lukacslacko/rolling_clock/designs/rolling-timer-p1s-light/bob-1mm/comparison-cad.png

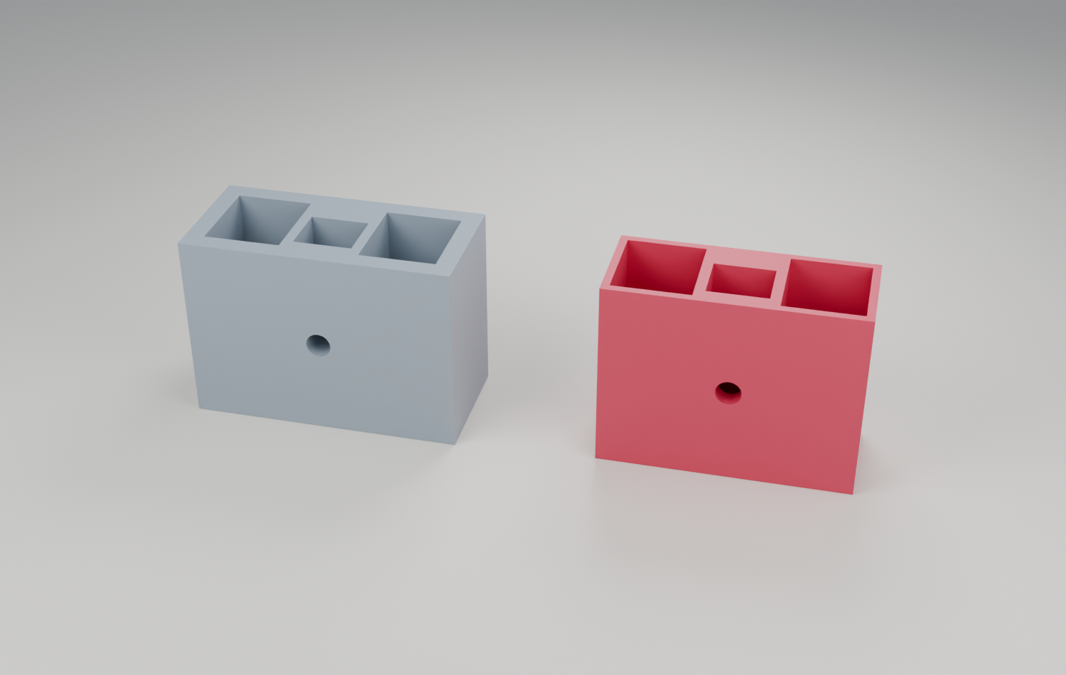
designs/rolling-timer-p1s-light/bob-1mm/comparison-cad.png
