lukacslacko/rolling_clock/designs/rolling-timer-p1s-light/bowl-bolt-section.png

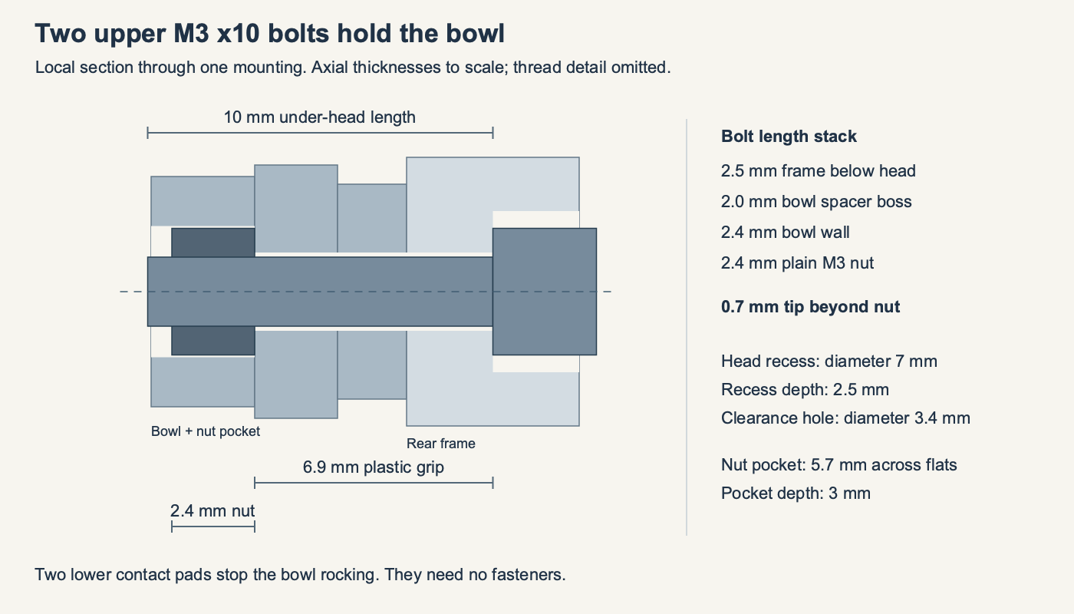
designs/rolling-timer-p1s-light/bowl-bolt-section.png
