lukacslacko/rolling_clock/designs/rolling-timer-p1s-light/fit-coupon.png

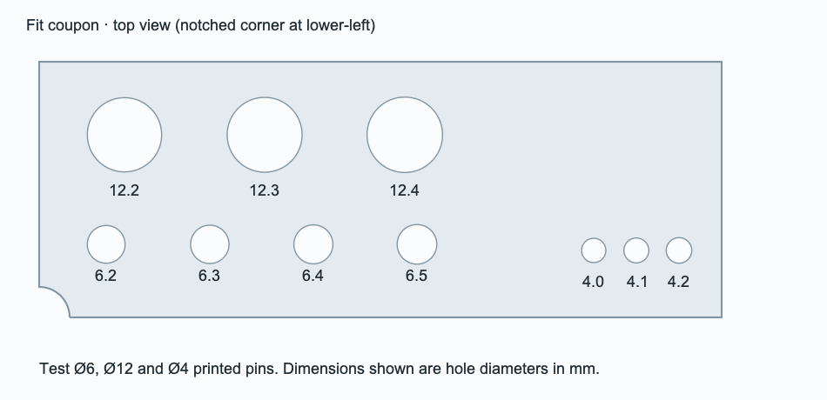
designs/rolling-timer-p1s-light/fit-coupon.png
