lukacslacko/rolling_clock/designs/rolling-timer-p1s-light/renders/light-mechanism.png

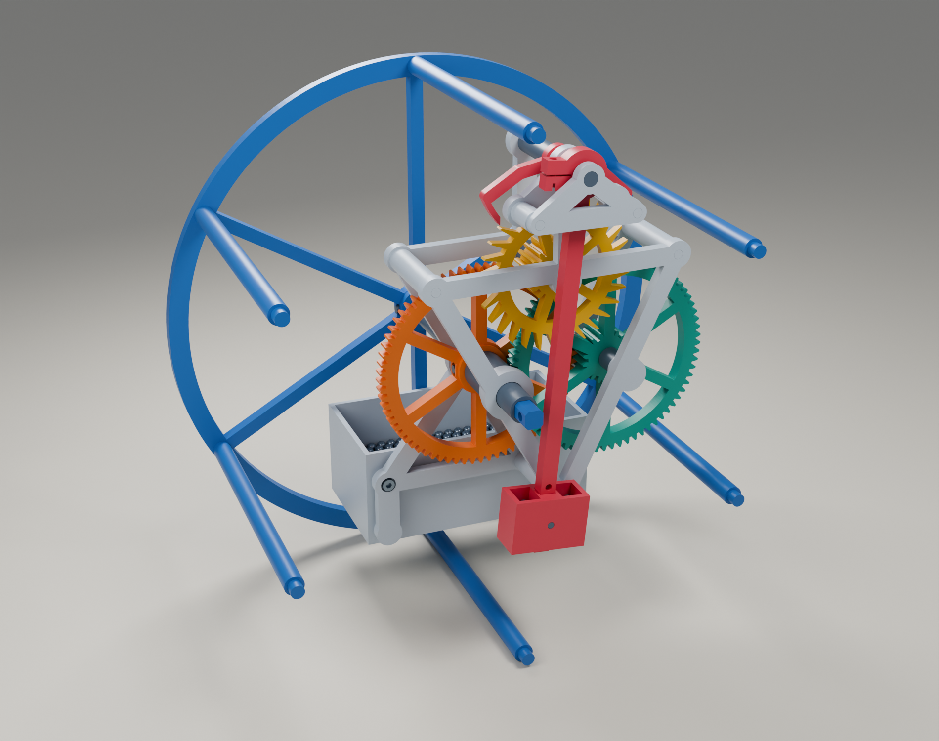
designs/rolling-timer-p1s-light/renders/light-mechanism.png
