lukacslacko/rolling_clock/designs/rolling-timer-p1s-light/renders/light-rear.png

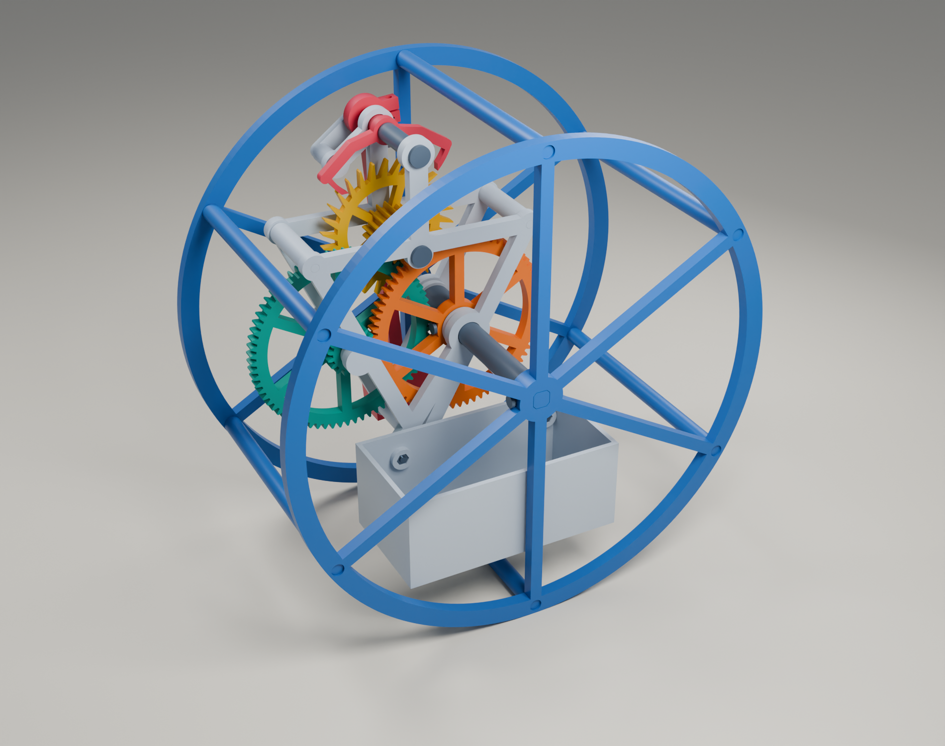
designs/rolling-timer-p1s-light/renders/light-rear.png
