lukacslacko/rolling_clock/designs/rolling-timer-p1s-r2/mounting-layout.png

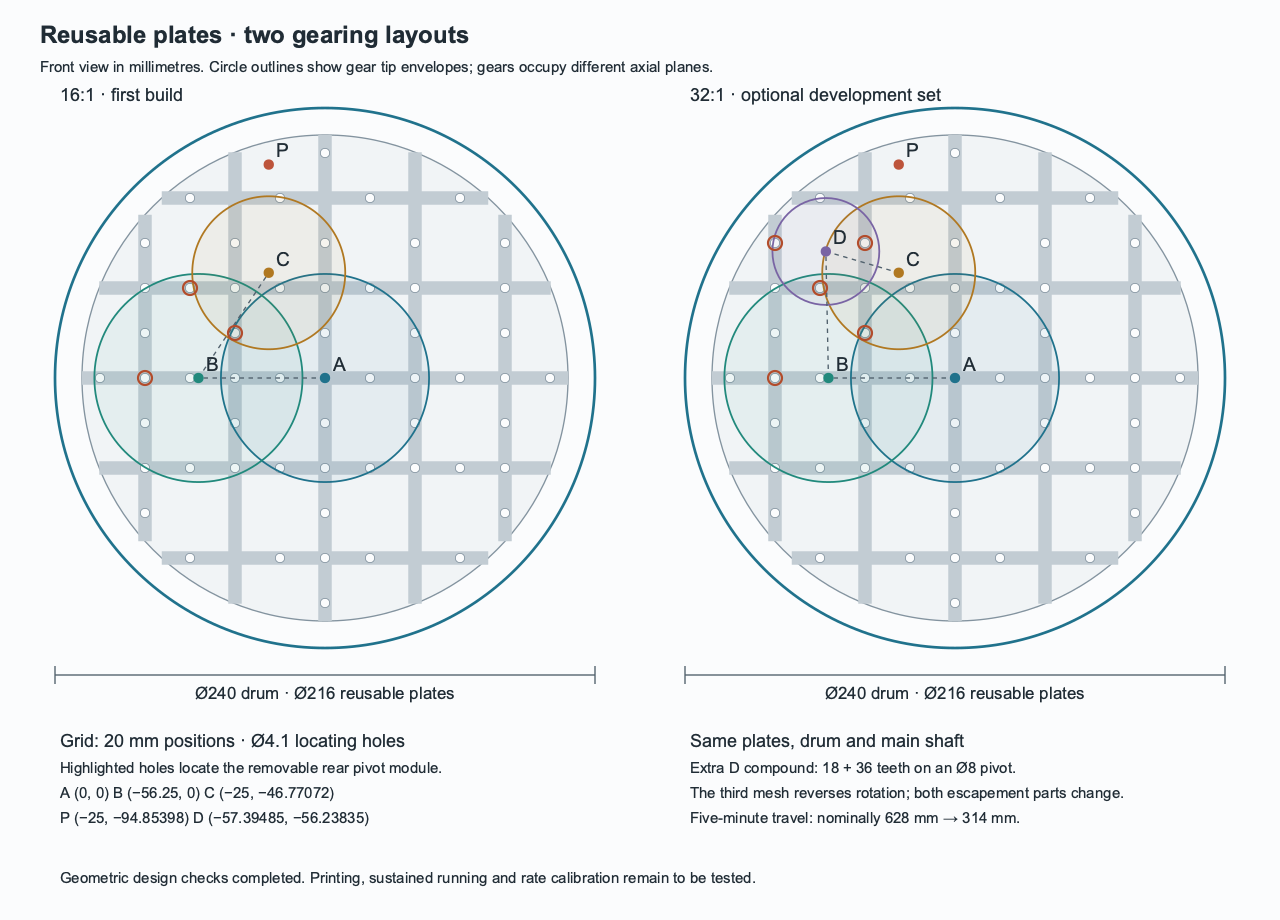
designs/rolling-timer-p1s-r2/mounting-layout.png
