lukacslacko/rolling_clock/designs/rolling-timer-p1s-r2/renders/perspective-rear.png

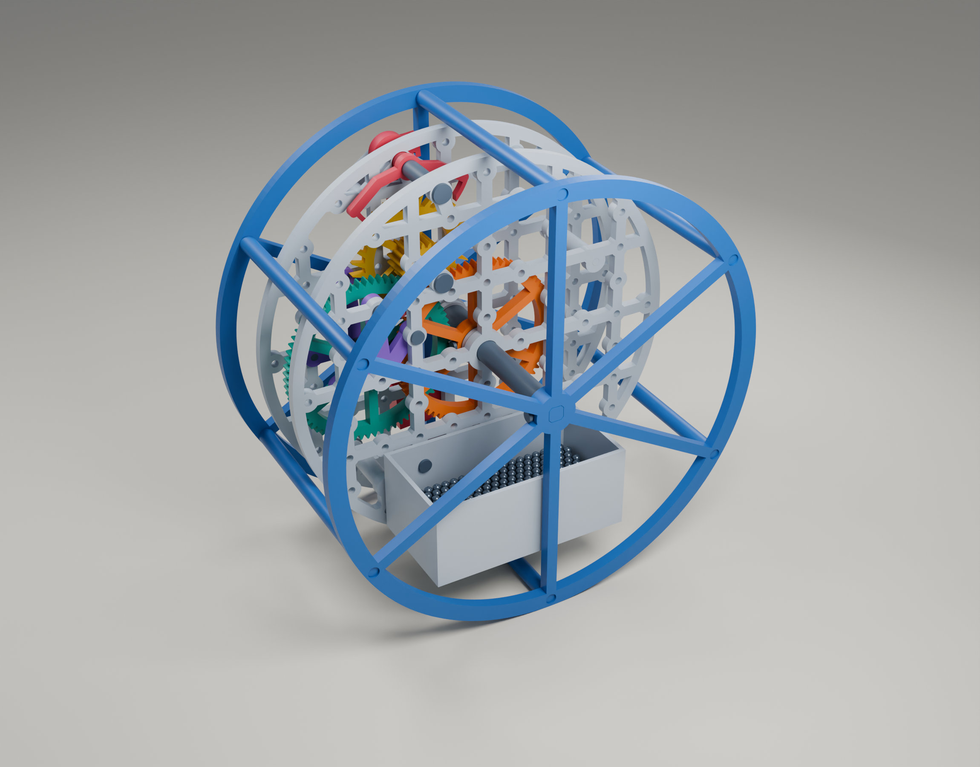
designs/rolling-timer-p1s-r2/renders/perspective-rear.png
