lukacslacko/rolling_clock/designs/rolling-timer-r3/renders/axle-detail.png

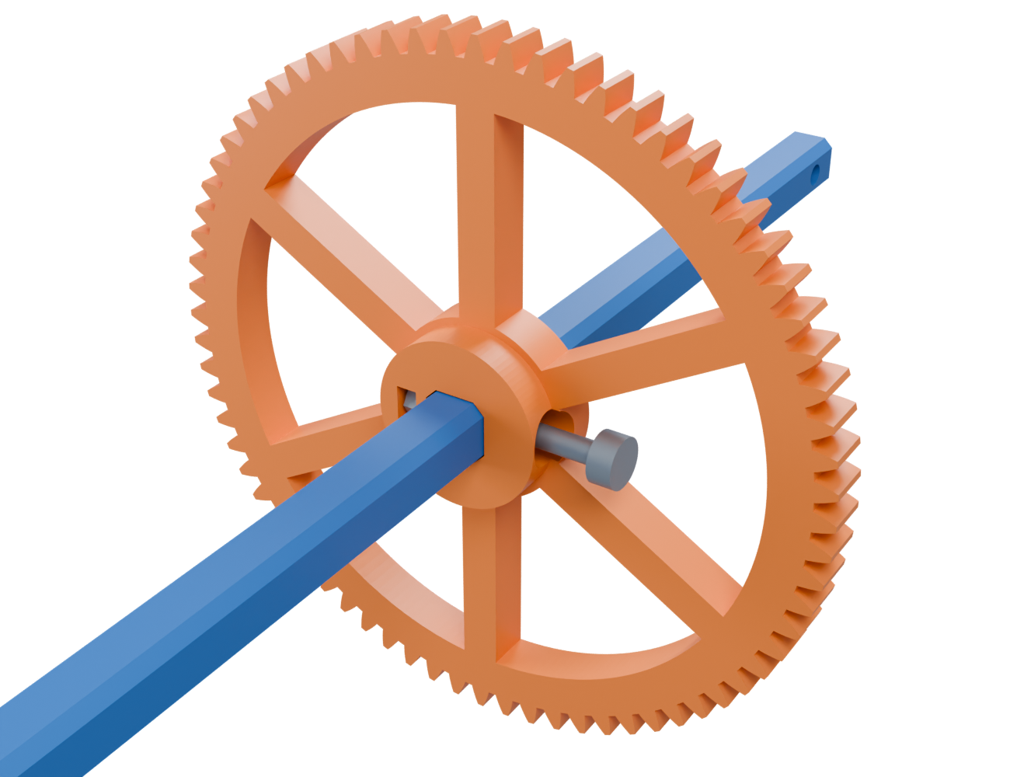
designs/rolling-timer-r3/renders/axle-detail.png
