lukacslacko/rolling_clock/designs/rolling-timer-r3/renders/bob-front-detail.png

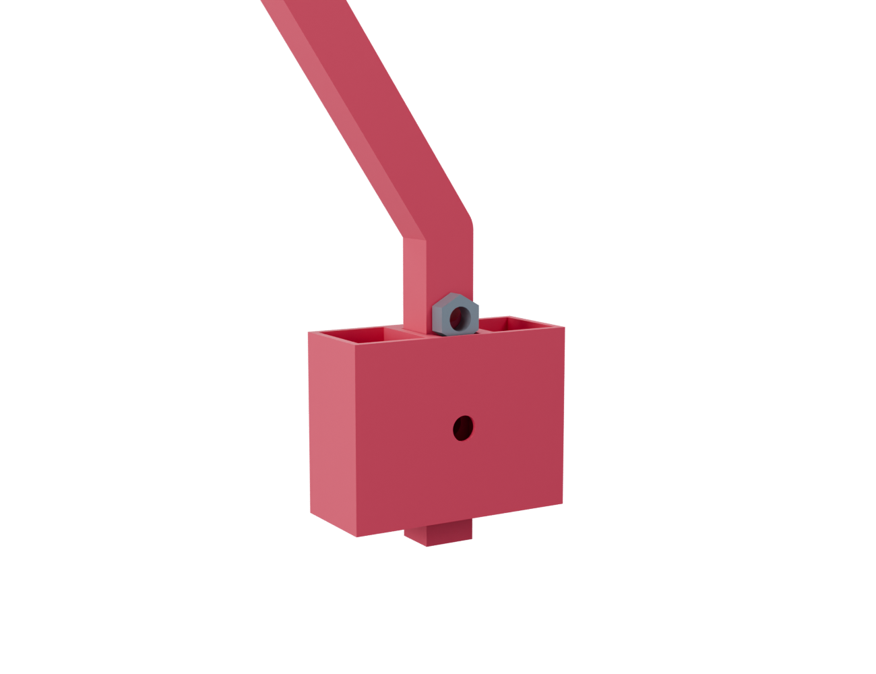
designs/rolling-timer-r3/renders/bob-front-detail.png
