lukacslacko/rolling_clock/designs/rolling-timer-r3/renders/case-post-detail.png

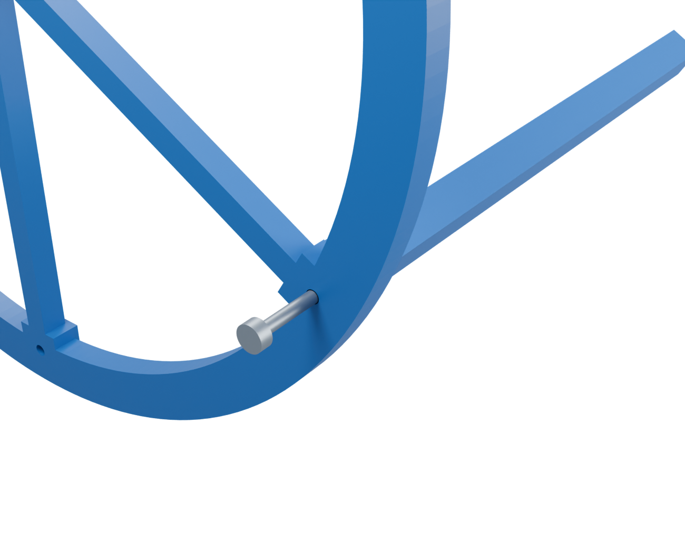
designs/rolling-timer-r3/renders/case-post-detail.png
