lukacslacko/rolling_clock/designs/rolling-timer-r3/renders/front-and-pendulum.png

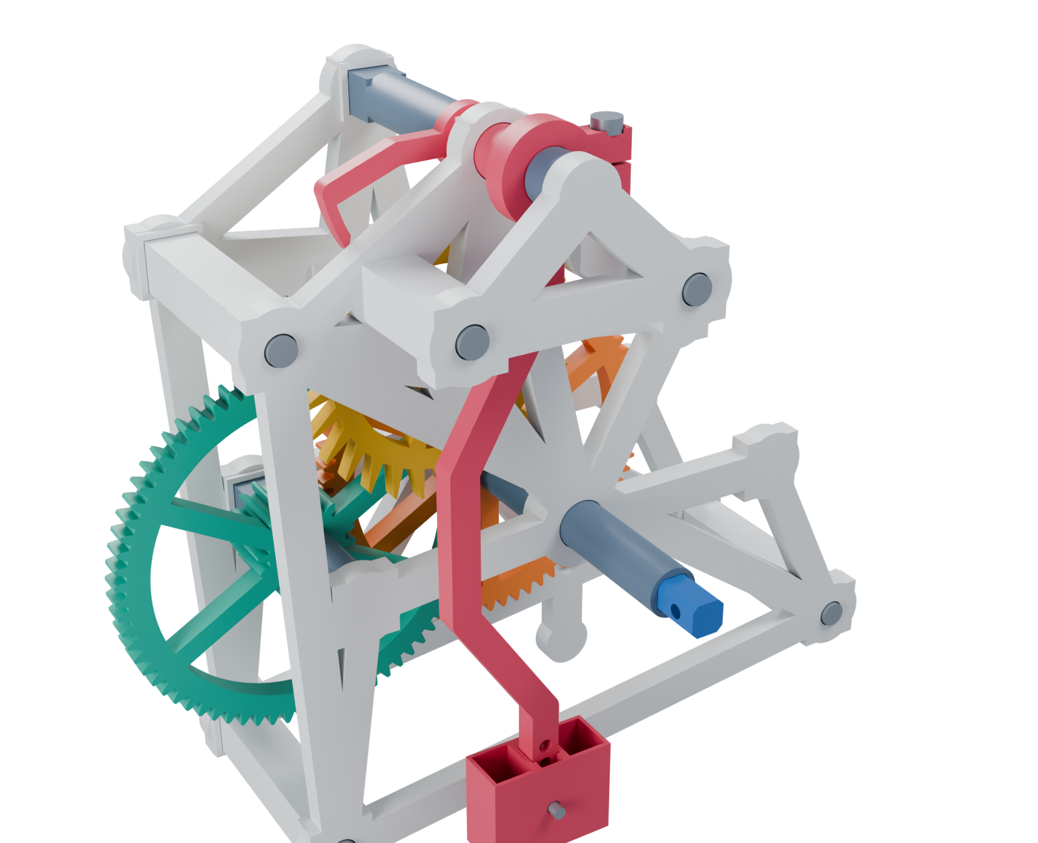
designs/rolling-timer-r3/renders/front-and-pendulum.png
