lukacslacko/rolling_clock/designs/rolling-timer-r3/renders/gear-stack.png

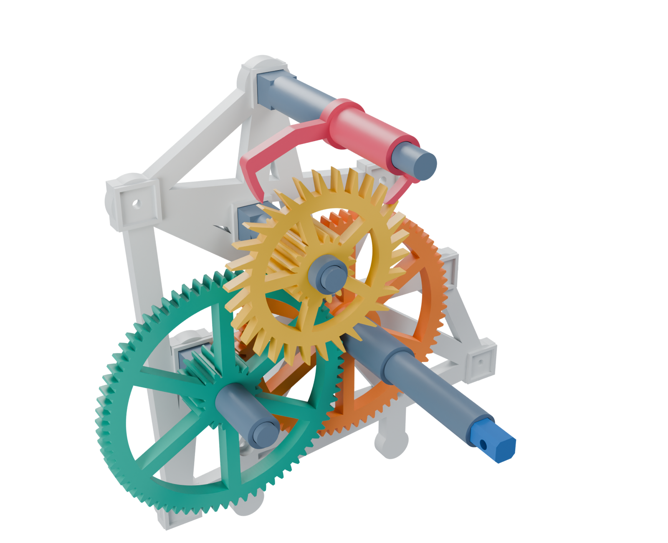
designs/rolling-timer-r3/renders/gear-stack.png
