lukacslacko/rolling_clock/designs/rolling-timer-r3/renders/mechanism-16x.png

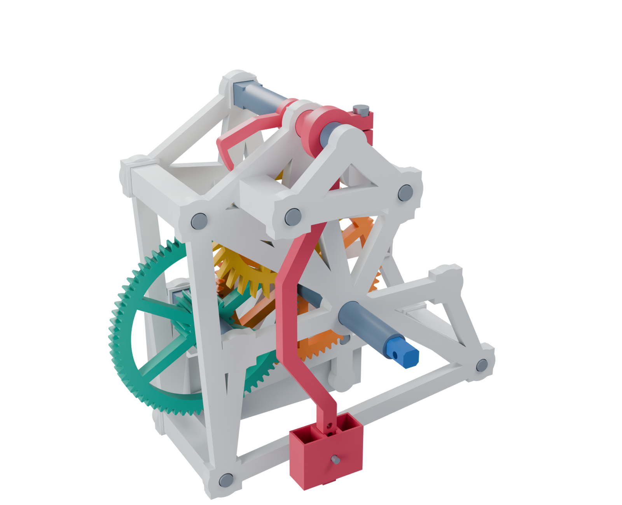
designs/rolling-timer-r3/renders/mechanism-16x.png
