lukacslacko/rolling_clock/designs/rolling-timer-p1s-r2/renders/square-drive-components.png

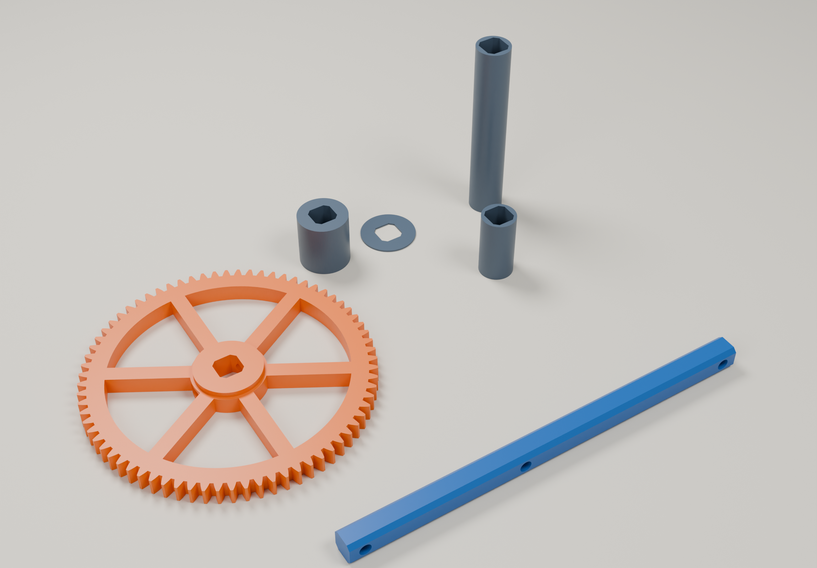
designs/rolling-timer-p1s-r2/renders/square-drive-components.png
