lukacslacko/rolling_clock/designs/rolling-timer-p1s-light/STL/30_fit_test_4mm.stl

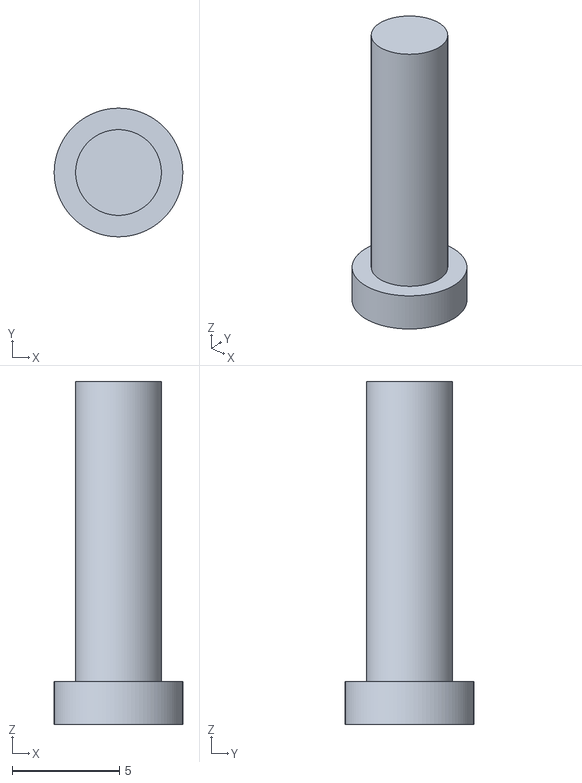
[picture p34: CAD file, 2026-10-01]
designs/rolling-timer-p1s-light/STL/30_fit_test_4mm.stl
6.00 x 6.00 x 16.0
