lukacslacko/rolling_clock/designs/rolling-timer-p1s-r2/source/assembly/24_11_compound_18_72.stl

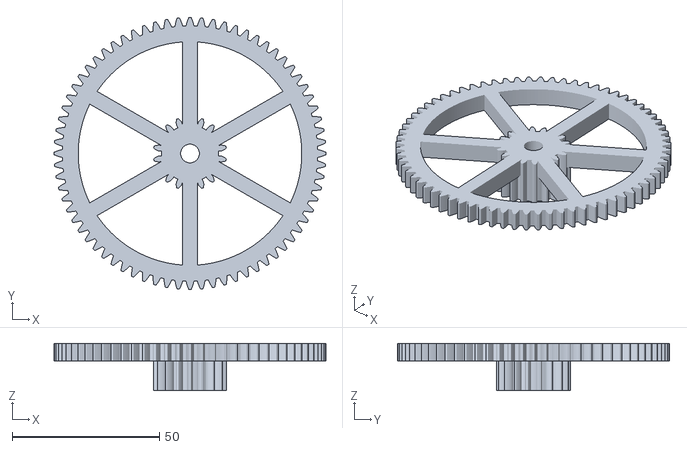
[picture p35: CAD file, 2026-10-01]
designs/rolling-timer-p1s-r2/source/assembly/24_11_compound_18_72.stl
92.5 x 92.5 x 16.0
