lukacslacko/rolling_clock/designs/rolling-timer-p1s-r2/upgrade-32x/STL/U11_D_recessed_collar.stl

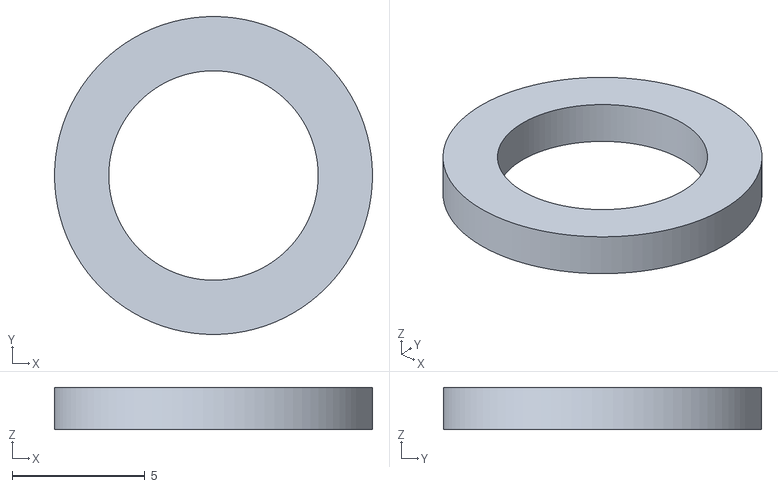
[picture p36: CAD file, 2026-10-01]
designs/rolling-timer-p1s-r2/upgrade-32x/STL/U11_D_recessed_collar.stl
12.0 x 12.0 x 1.60
