lukacslacko/rolling_clock/designs/rolling-timer-r3/assembly/16x/01_front_case_wheel.stl

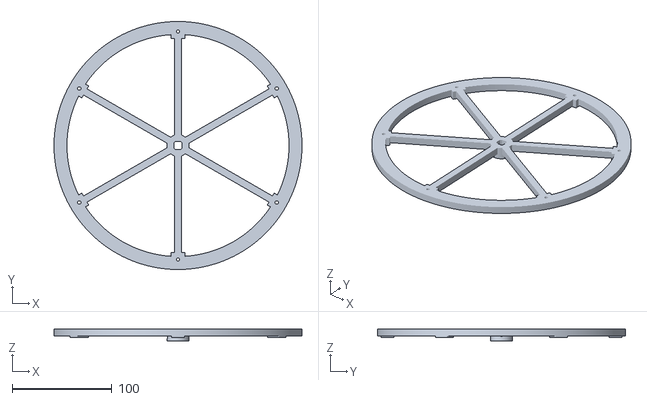
[picture p37: CAD file, 2026-10-08]
designs/rolling-timer-r3/assembly/16x/01_front_case_wheel.stl
248.0 x 248.0 x 12.0
