lukacslacko/rolling_clock/designs/rolling-timer-r3/STL/16x/11_B_18_72.stl

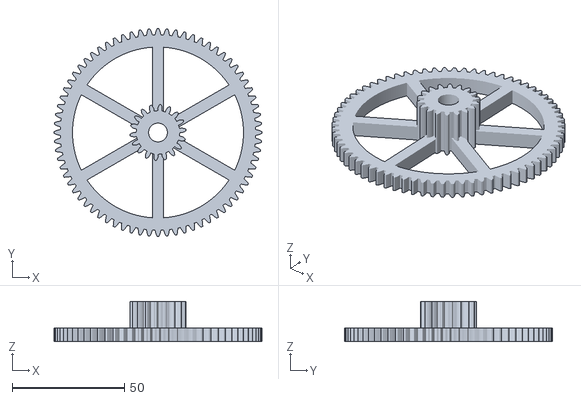
[picture p38: CAD file, 2026-10-02]
designs/rolling-timer-r3/STL/16x/11_B_18_72.stl
92.5 x 92.5 x 18.0
