lukacslacko/rolling_clock/designs/rolling-timer-r3/STL/32x/27_C_front_spacer.stl

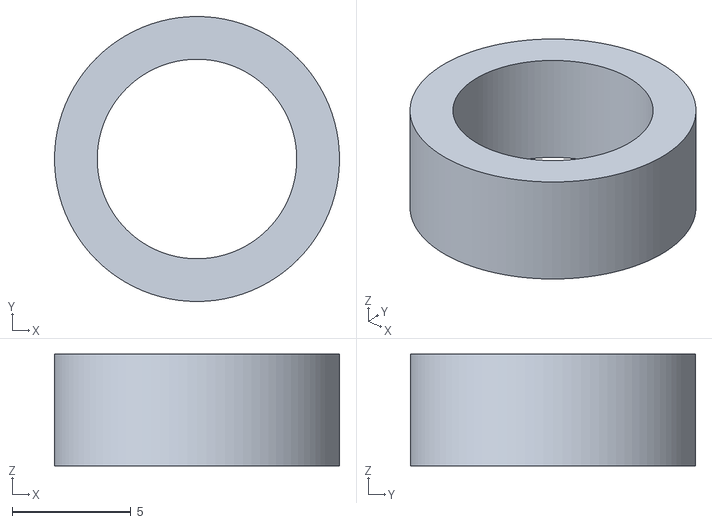
[picture p39: CAD file, 2026-10-02]
designs/rolling-timer-r3/STL/32x/27_C_front_spacer.stl
12.0 x 12.0 x 4.70
