lukacslacko/rolling_clock/designs/rolling-timer-r3/STL/slow-common/18_anchor_reversed.stl

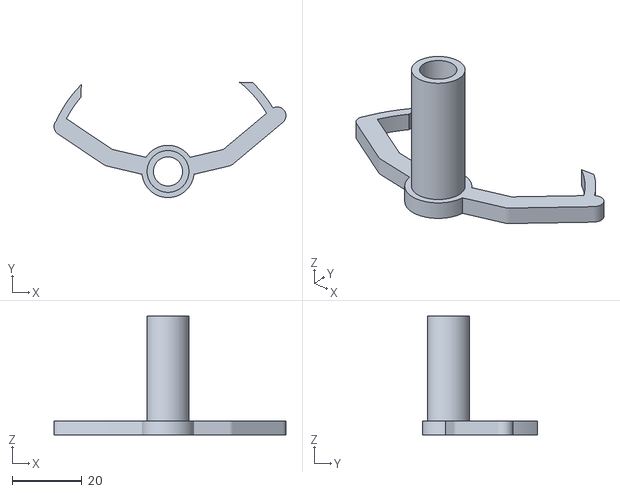
[picture p40: CAD file, 2026-10-02]
designs/rolling-timer-r3/STL/slow-common/18_anchor_reversed.stl
66.5 x 33.0 x 34.0
