lukacslacko/rolling_clock/designs/rolling-timer-p1s-light/bob-1mm/25_open_pendulum_bob_1mm.stl

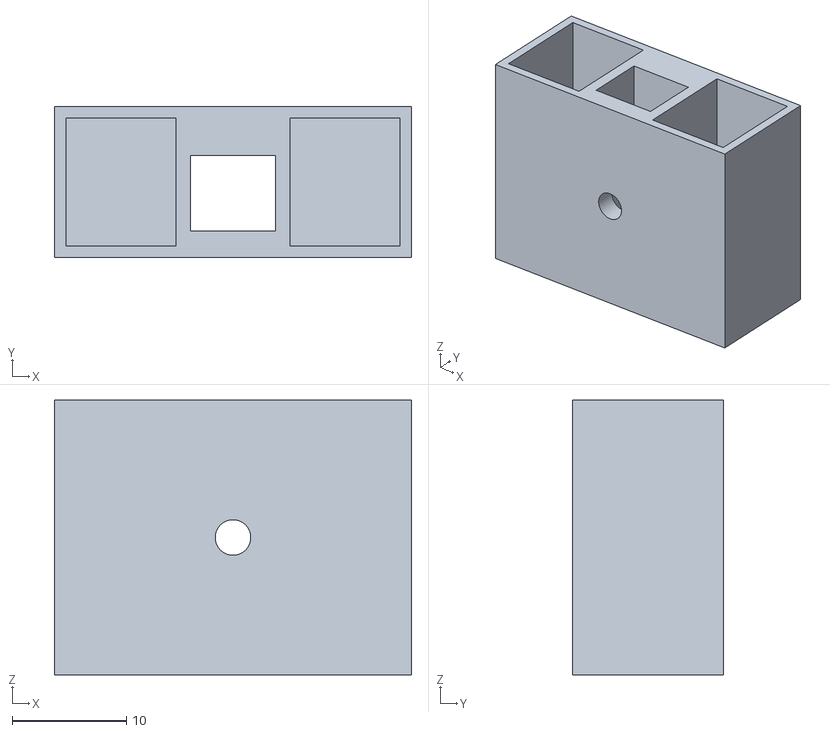
[picture p41: CAD file, 2026-10-01]
designs/rolling-timer-p1s-light/bob-1mm/25_open_pendulum_bob_1mm.stl
31.2 x 13.2 x 24.0
