lukacslacko/rolling_clock/designs/rolling-timer-p1s-light/source/assembly/03_02_case_post.stl

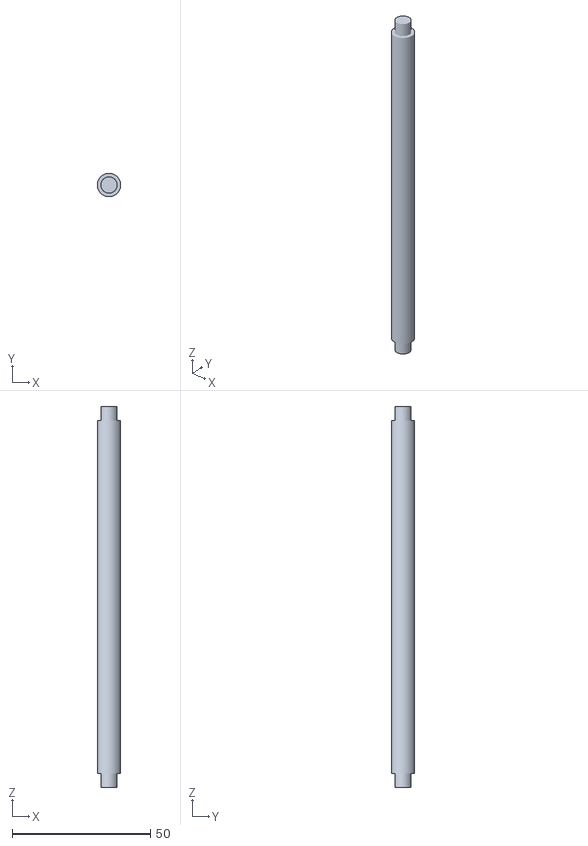
[picture p42: CAD file, 2026-10-01]
designs/rolling-timer-p1s-light/source/assembly/03_02_case_post.stl
8.50 x 8.50 x 138.0
