lukacslacko/rolling_clock/designs/rolling-timer-p1s-light/STL/01_case_wheel.stl

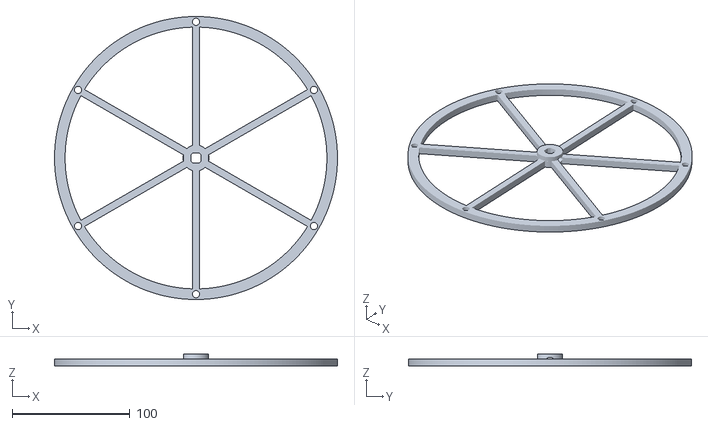
[picture p43: CAD file, 2026-10-01]
designs/rolling-timer-p1s-light/STL/01_case_wheel.stl
240.0 x 240.0 x 10.0
