lukacslacko/rolling_clock/designs/rolling-timer-p1s-r2/source/assembly/27_31_B_rear_pivot_module.stl

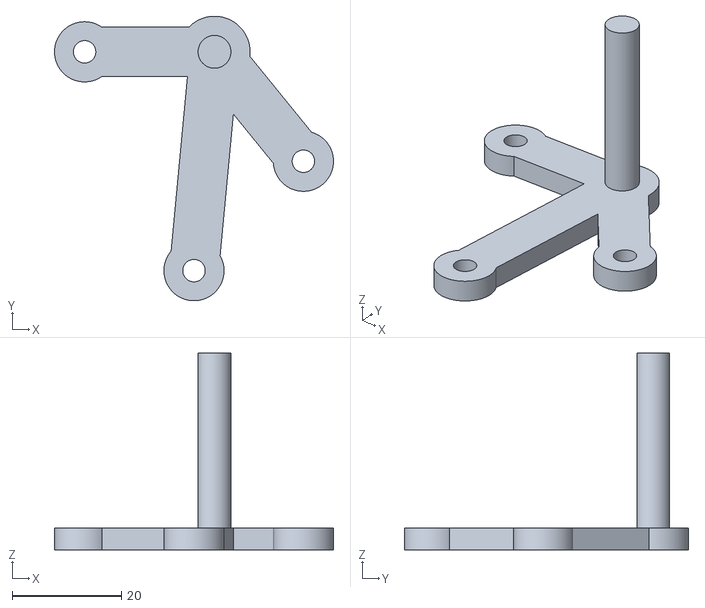
[picture p44: CAD file, 2026-10-01]
designs/rolling-timer-p1s-r2/source/assembly/27_31_B_rear_pivot_module.stl
51.0 x 52.0 x 36.0
