lukacslacko/rolling_clock/designs/rolling-timer-p1s-r2/STL/27_fit_coupon.stl

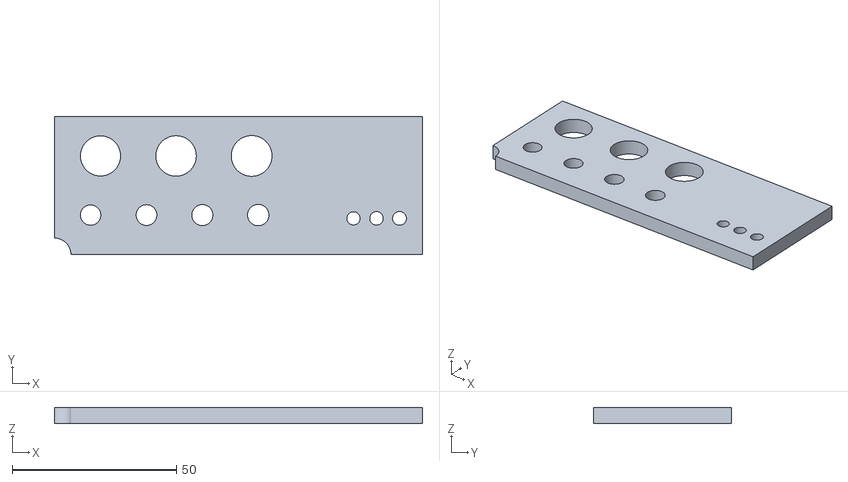
[picture p45: CAD file, 2026-10-01]
designs/rolling-timer-p1s-r2/STL/27_fit_coupon.stl
112.0 x 42.0 x 5.00
