lukacslacko/rolling_clock/designs/rolling-timer-p1s-r2/upgrade-32x/STL/U10_D_rear_spacer.stl

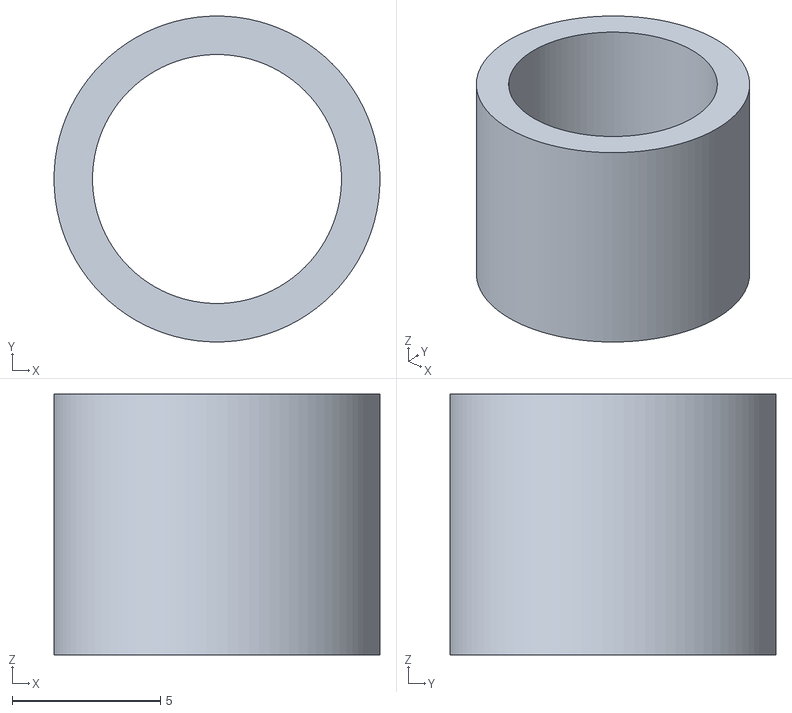
[picture p46: CAD file, 2026-10-01]
designs/rolling-timer-p1s-r2/upgrade-32x/STL/U10_D_rear_spacer.stl
11.0 x 11.0 x 8.80
