lukacslacko/rolling_clock/designs/rolling-timer-r3/STL/64x/12_escape_compound.stl

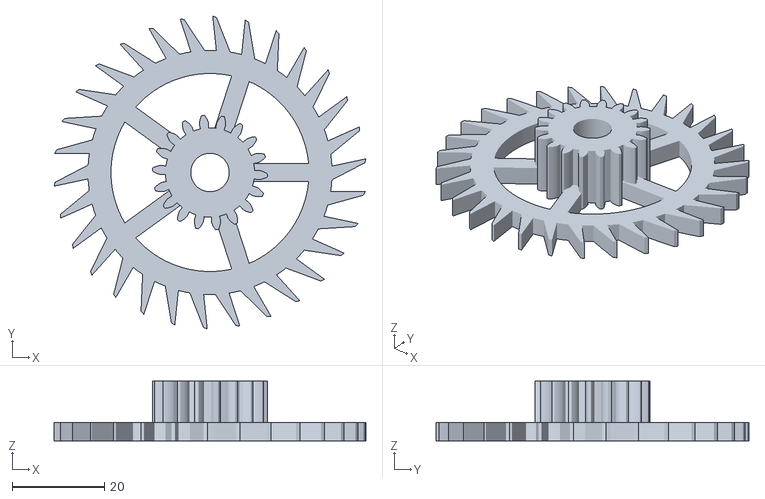
[picture p47: CAD file, 2026-10-02]
designs/rolling-timer-r3/STL/64x/12_escape_compound.stl
67.7 x 68.0 x 13.0
