lukacslacko/rolling_clock/designs/rolling-timer-r3/STL/common/38_rear_journal_thrust_collar.stl

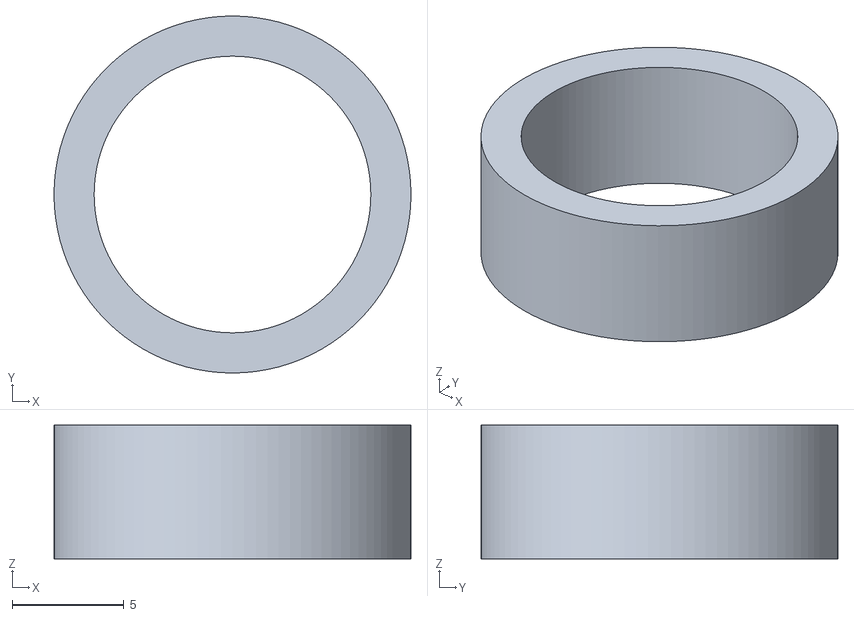
[picture p48: CAD file, 2026-10-08]
designs/rolling-timer-r3/STL/common/38_rear_journal_thrust_collar.stl
16.0 x 16.0 x 6.00
