lukacslacko/rolling_clock/designs/rolling-timer-p1s-light/source/assembly/17_08_open_ballast_bucket.stl

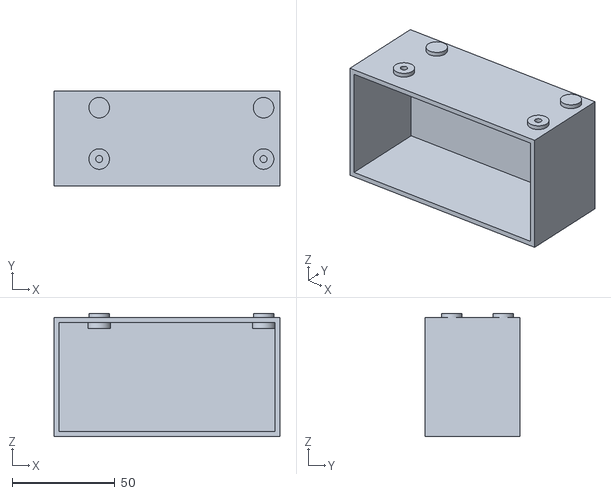
[picture p49: CAD file, 2026-10-01]
designs/rolling-timer-p1s-light/source/assembly/17_08_open_ballast_bucket.stl
110.0 x 46.0 x 60.0
