lukacslacko/rolling_clock/designs/rolling-timer-p1s-light/STL/05_rear_carrier.stl

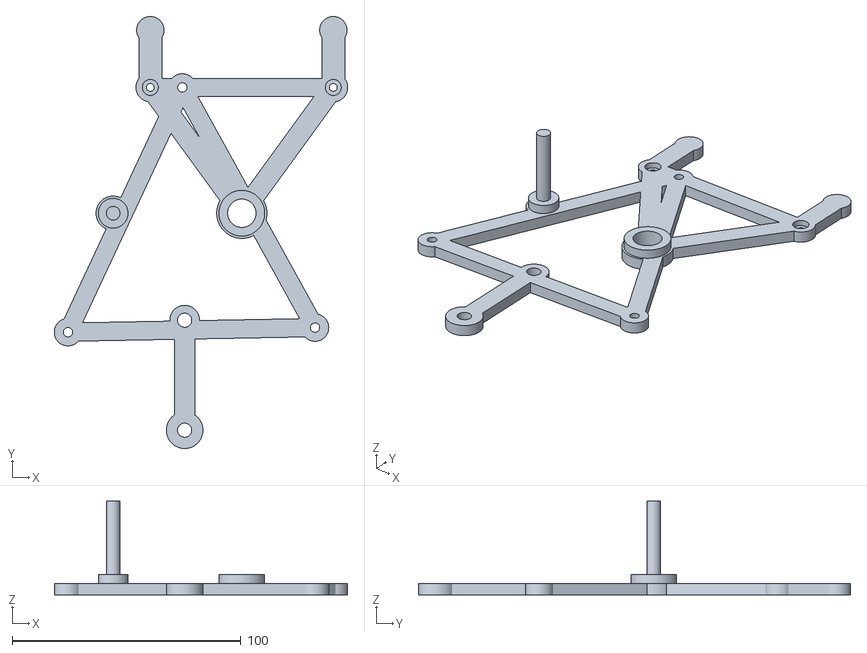
[picture p50: CAD file, 2026-10-01]
designs/rolling-timer-p1s-light/STL/05_rear_carrier.stl
128.3 x 188.9 x 41.0
