lukacslacko/rolling_clock/designs/rolling-timer-p1s-r2/source/assembly/17_07_carrier_post.stl

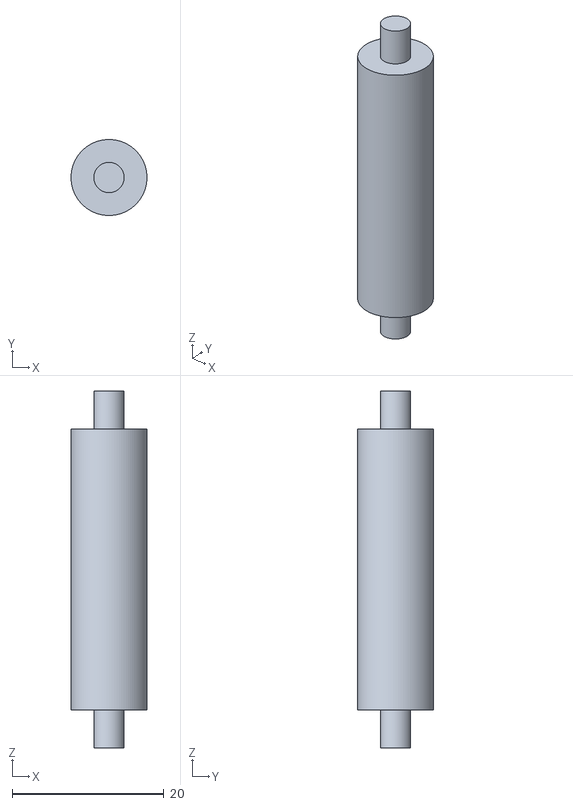
[picture p51: CAD file, 2026-10-01]
designs/rolling-timer-p1s-r2/source/assembly/17_07_carrier_post.stl
10.0 x 10.0 x 47.0
