lukacslacko/rolling_clock/designs/rolling-timer-p1s-r2/STL/20_anchor_rear_spacer.stl

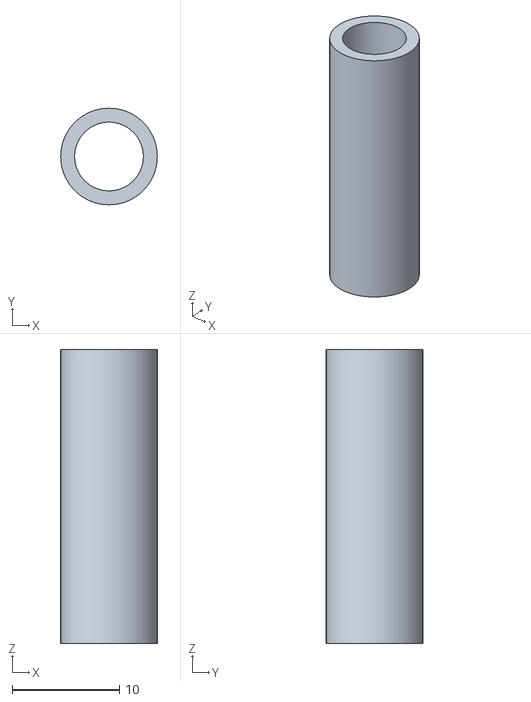
[picture p52: CAD file, 2026-10-01]
designs/rolling-timer-p1s-r2/STL/20_anchor_rear_spacer.stl
9.00 x 9.00 x 27.4
