lukacslacko/rolling_clock/designs/rolling-timer-p1s-r2/upgrade-32x/STL/U04_reversed_escape_compound.stl

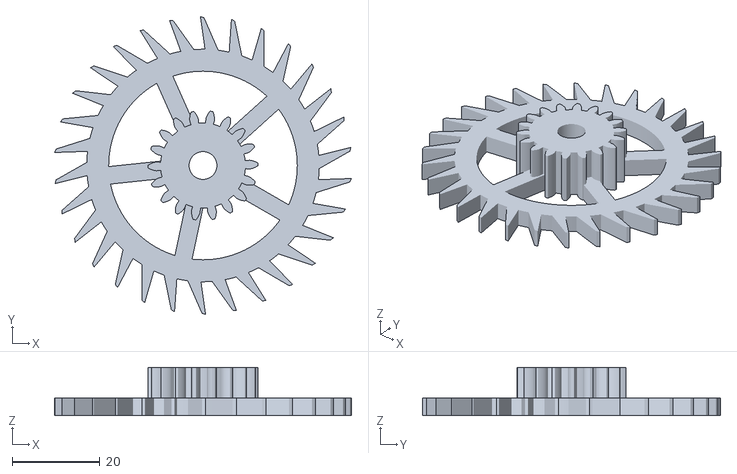
[picture p53: CAD file, 2026-10-01]
designs/rolling-timer-p1s-r2/upgrade-32x/STL/U04_reversed_escape_compound.stl
67.7 x 68.0 x 11.0
