lukacslacko/rolling_clock/designs/rolling-timer-r3/STL/16x/12_escape_compound.stl

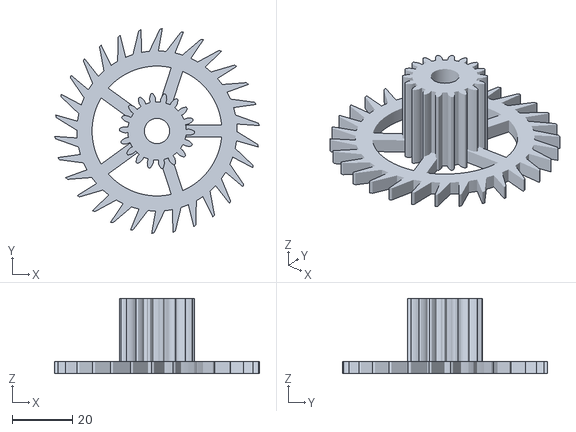
[picture p54: CAD file, 2026-10-02]
designs/rolling-timer-r3/STL/16x/12_escape_compound.stl
67.9 x 67.9 x 25.0
