lukacslacko/rolling_clock/designs/rolling-timer-r3/STL/common/07_square_frame_post.stl

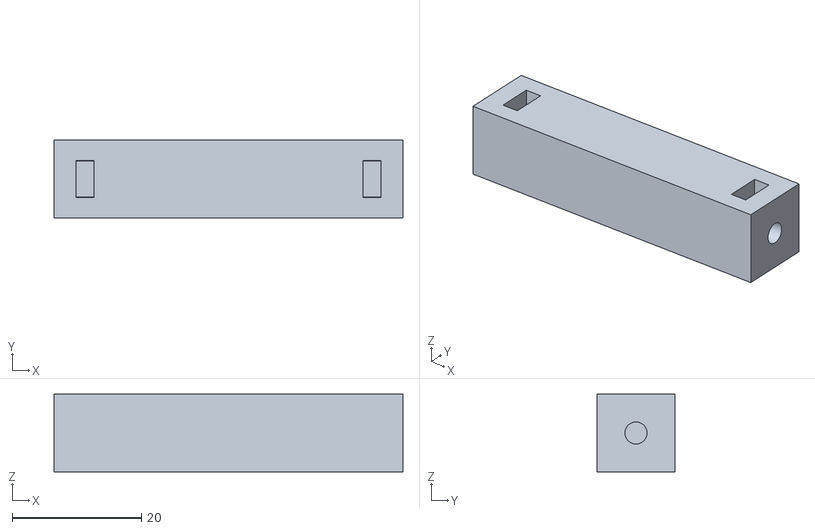
[picture p56: CAD file, 2026-10-07]
designs/rolling-timer-r3/STL/common/07_square_frame_post.stl
54.0 x 12.0 x 12.0
