lukacslacko/rolling_clock/designs/rolling-timer-p1s-light/source/assembly/20_12_escape_compound.stl

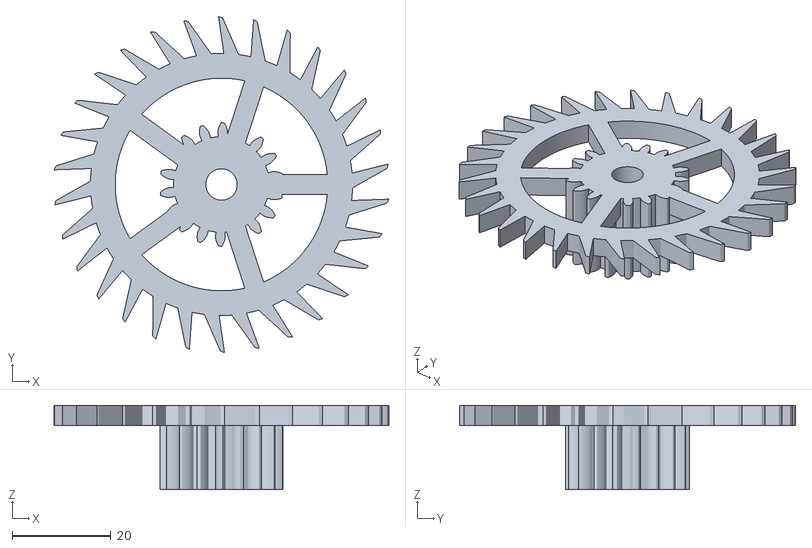
[picture p57: CAD file, 2026-10-01]
designs/rolling-timer-p1s-light/source/assembly/20_12_escape_compound.stl
67.7 x 68.0 x 17.0
