lukacslacko/rolling_clock/designs/rolling-timer-p1s-light/STL/29_fit_test_12mm.stl

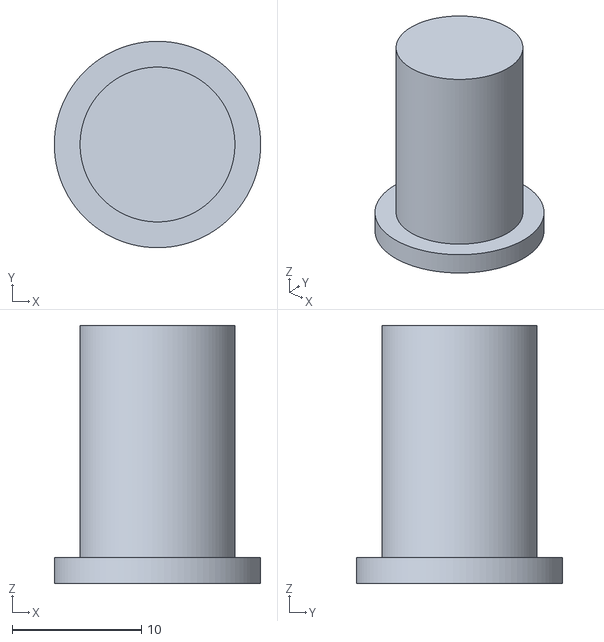
[picture p58: CAD file, 2026-10-01]
designs/rolling-timer-p1s-light/STL/29_fit_test_12mm.stl
16.0 x 16.0 x 20.0
