lukacslacko/rolling_clock/designs/rolling-timer-p1s-r2/source/assembly/46_23_bridge_post.stl

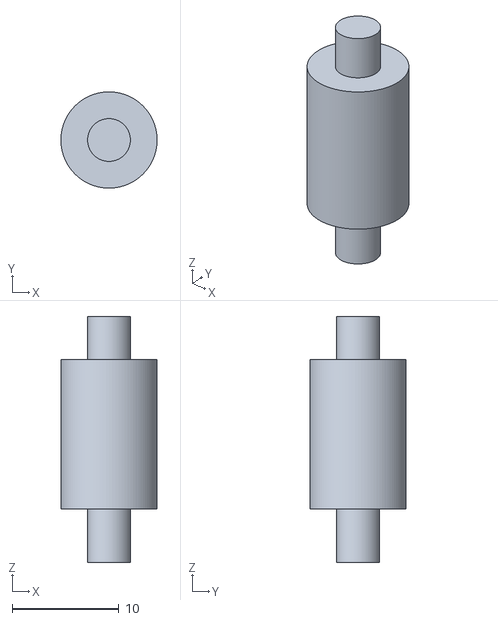
[picture p59: CAD file, 2026-10-01]
designs/rolling-timer-p1s-r2/source/assembly/46_23_bridge_post.stl
9.00 x 9.00 x 23.0
