lukacslacko/rolling_clock/designs/rolling-timer-p1s-r2/upgrade-32x/STL/U05_reversed_anchor.stl

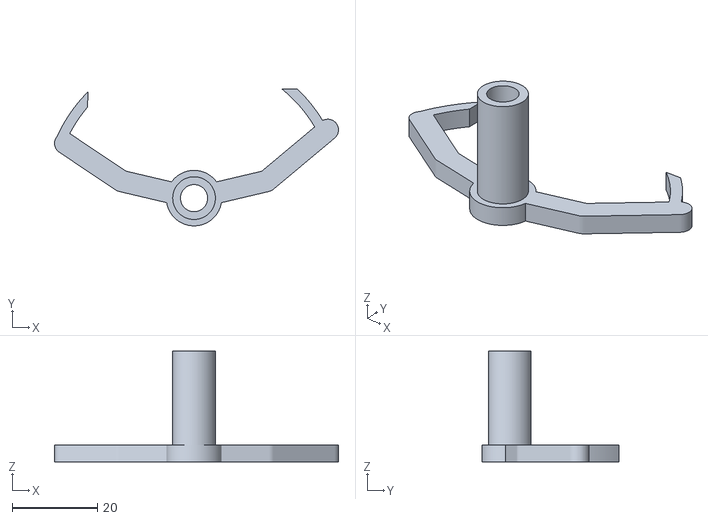
[picture p60: CAD file, 2026-10-01]
designs/rolling-timer-p1s-r2/upgrade-32x/STL/U05_reversed_anchor.stl
66.5 x 32.0 x 26.0
