lukacslacko/rolling_clock/designs/rolling-timer-r3/assembly/16x/93_pendulum_clamp.stl

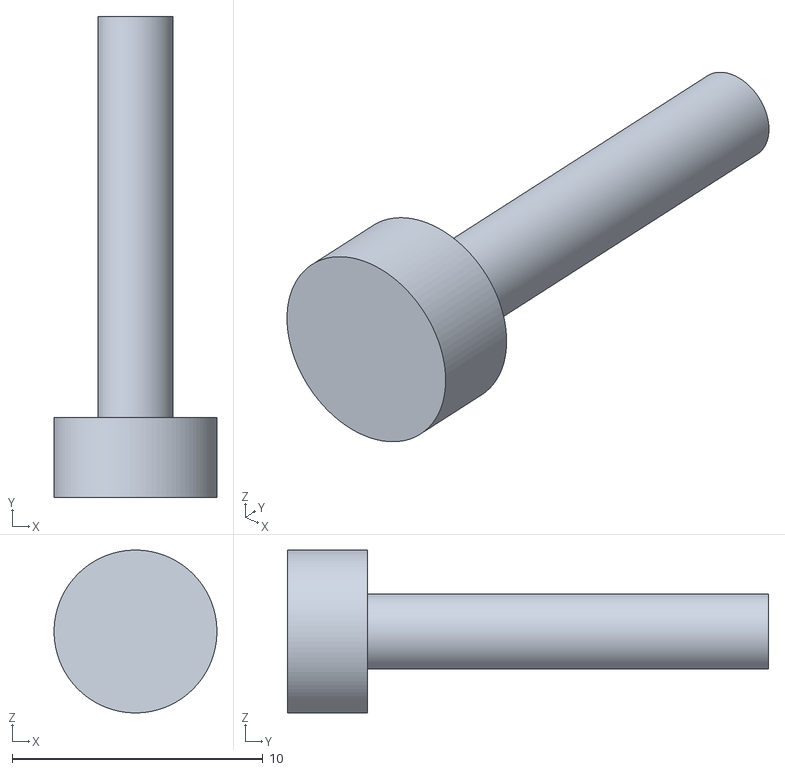
[picture p61: CAD file, 2026-10-07]
designs/rolling-timer-r3/assembly/16x/93_pendulum_clamp.stl
6.50 x 19.2 x 6.50
