lukacslacko/rolling_clock/designs/rolling-timer-r3/assembly/32x/75_12_escape_compound.stl

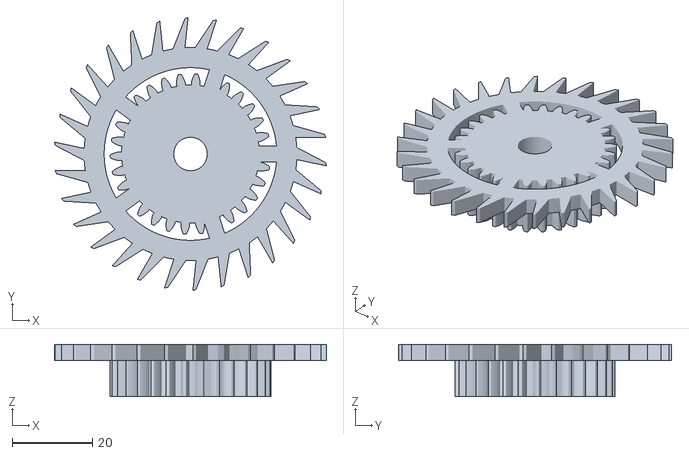
[picture p62: CAD file, 2026-10-07]
designs/rolling-timer-r3/assembly/32x/75_12_escape_compound.stl
67.7 x 68.0 x 13.0
