lukacslacko/rolling_clock/designs/rolling-timer-r3/assembly/64x/44_frame_front_0.stl

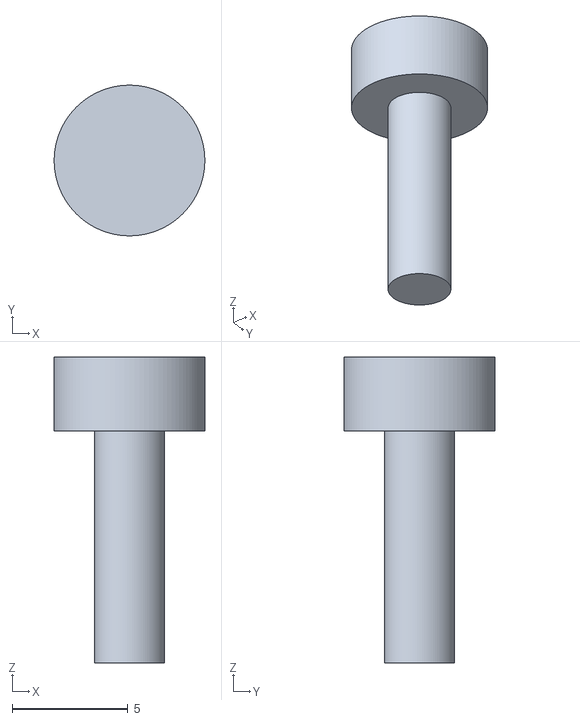
[picture p63: CAD file, 2026-10-07]
designs/rolling-timer-r3/assembly/64x/44_frame_front_0.stl
6.50 x 6.50 x 13.2
