lukacslacko/rolling_clock/designs/rolling-timer-r3/STL/32x/14_D_18_60.stl

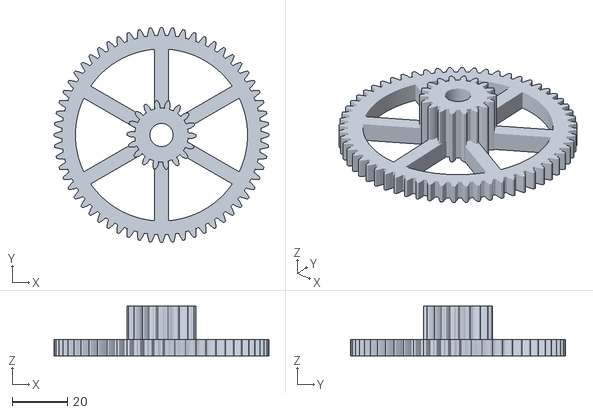
[picture p64: CAD file, 2026-10-02]
designs/rolling-timer-r3/STL/32x/14_D_18_60.stl
77.5 x 77.5 x 18.0
