lukacslacko/rolling_clock/designs/rolling-timer-r3/STL/64x/17_C_rear_spacer.stl

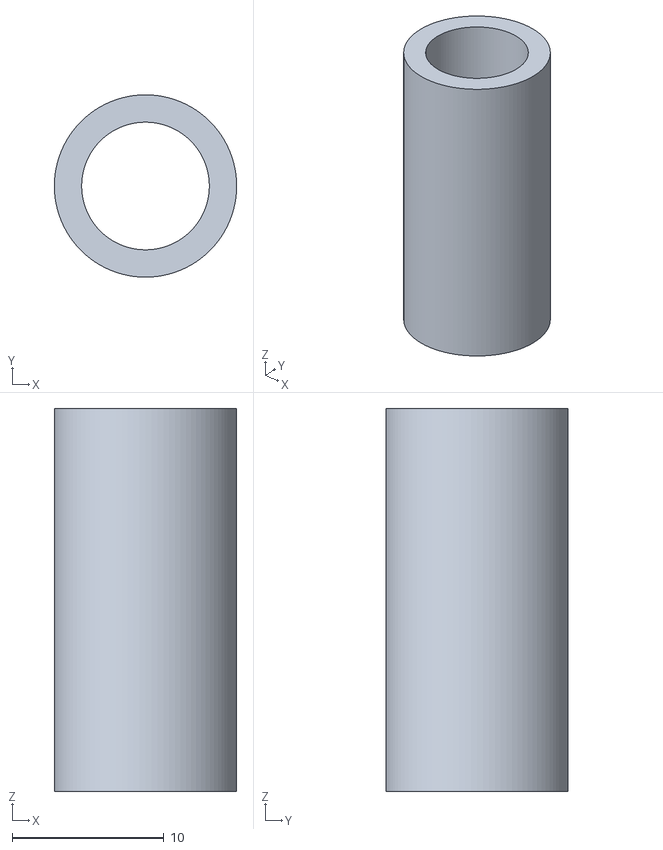
[picture p65: CAD file, 2026-10-02]
designs/rolling-timer-r3/STL/64x/17_C_rear_spacer.stl
12.0 x 12.0 x 25.2
