lukacslacko/rolling_clock/designs/rolling-timer-r3/STL/common/02_square_case_post.stl

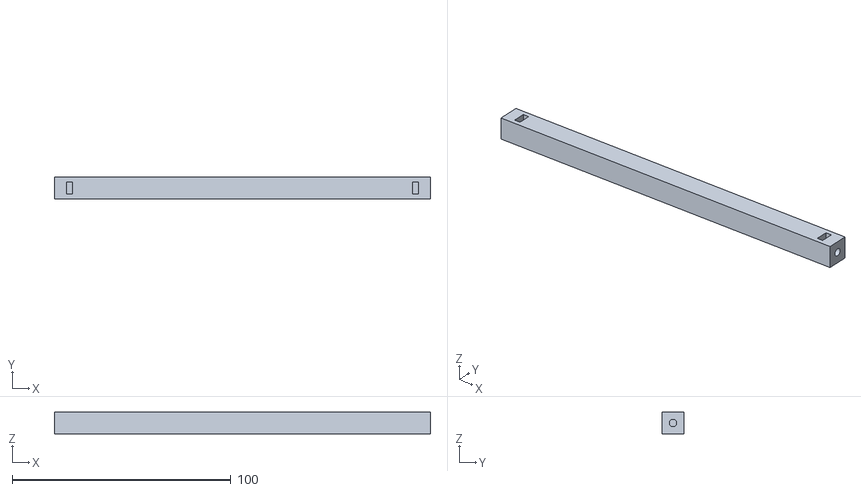
[picture p66: CAD file, 2026-10-07]
designs/rolling-timer-r3/STL/common/02_square_case_post.stl
172.0 x 10.0 x 10.0
