lukacslacko/rolling_clock/designs/rolling-timer-r3/STL/fit-tests/41_post_seat_coupon.stl

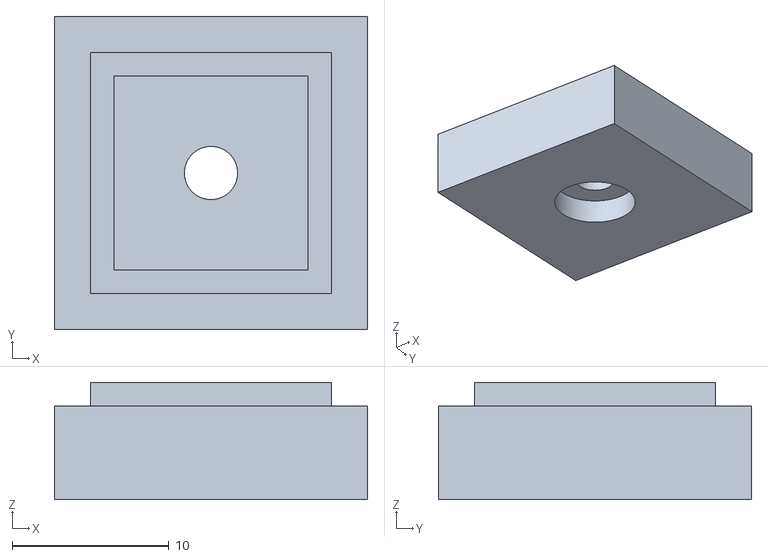
[picture p67: CAD file, 2026-10-02]
designs/rolling-timer-r3/STL/fit-tests/41_post_seat_coupon.stl
20.0 x 20.0 x 7.50
