lukacslacko/rolling_clock/designs/rolling-timer-p1s-light/source/assembly/21_13_gear_pivot.stl

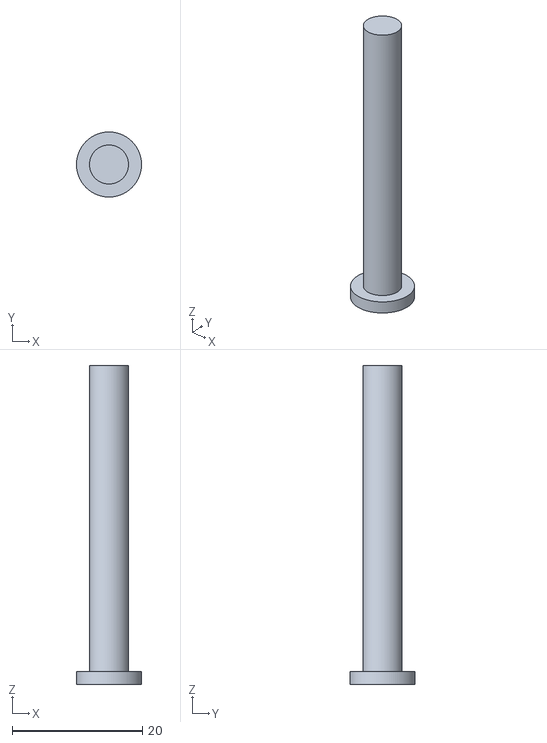
[picture p68: CAD file, 2026-10-01]
designs/rolling-timer-p1s-light/source/assembly/21_13_gear_pivot.stl
10.0 x 10.0 x 49.0
