lukacslacko/rolling_clock/designs/rolling-timer-p1s-light/STL/17_C_front_spacer.stl

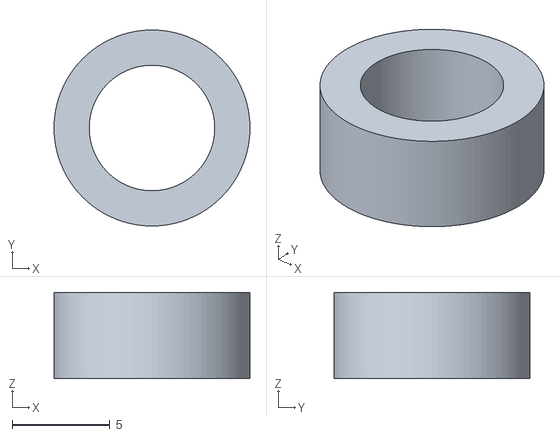
[picture p69: CAD file, 2026-10-01]
designs/rolling-timer-p1s-light/STL/17_C_front_spacer.stl
10.0 x 10.0 x 4.40
