lukacslacko/rolling_clock/designs/rolling-timer-p1s-r2/source/assembly/18_08_open_ballast_bucket.stl

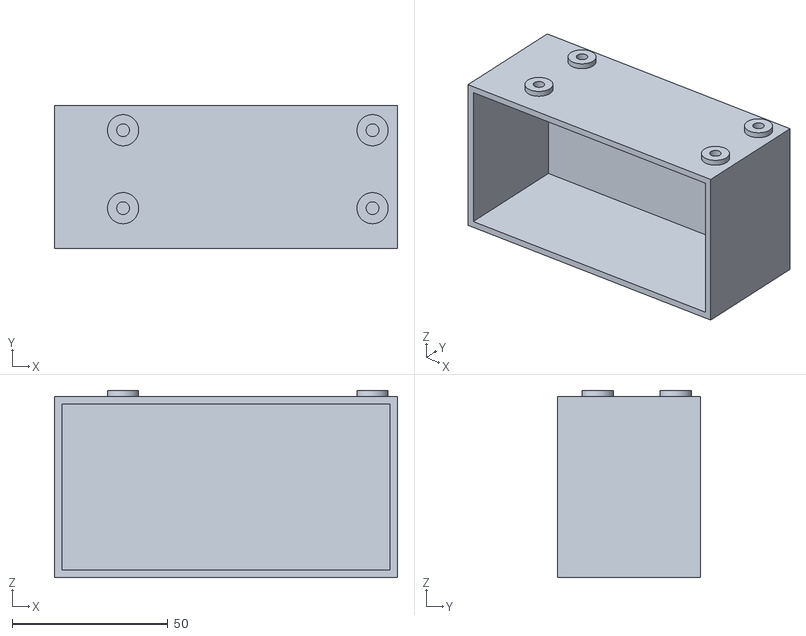
[picture p70: CAD file, 2026-10-01]
designs/rolling-timer-p1s-r2/source/assembly/18_08_open_ballast_bucket.stl
110.0 x 46.0 x 60.0
