lukacslacko/rolling_clock/designs/rolling-timer-p1s-r2/upgrade-32x/STL/U02_B_compound.stl

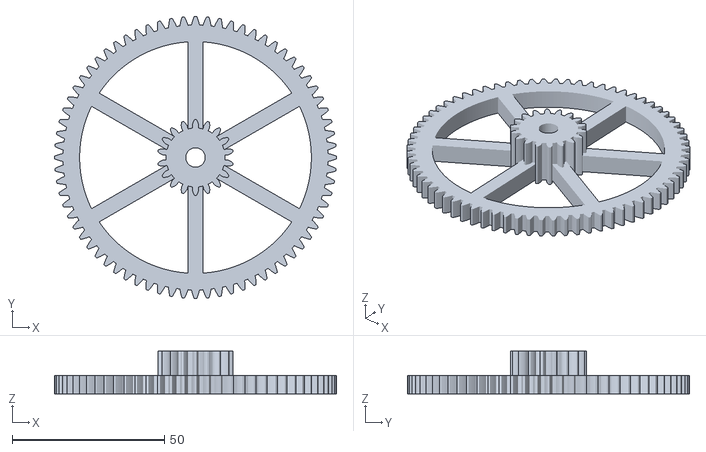
[picture p71: CAD file, 2026-10-01]
designs/rolling-timer-p1s-r2/upgrade-32x/STL/U02_B_compound.stl
92.5 x 92.5 x 14.0
