lukacslacko/rolling_clock/designs/rolling-timer-p1s-r2/source/assembly/32_33_module_pin.stl

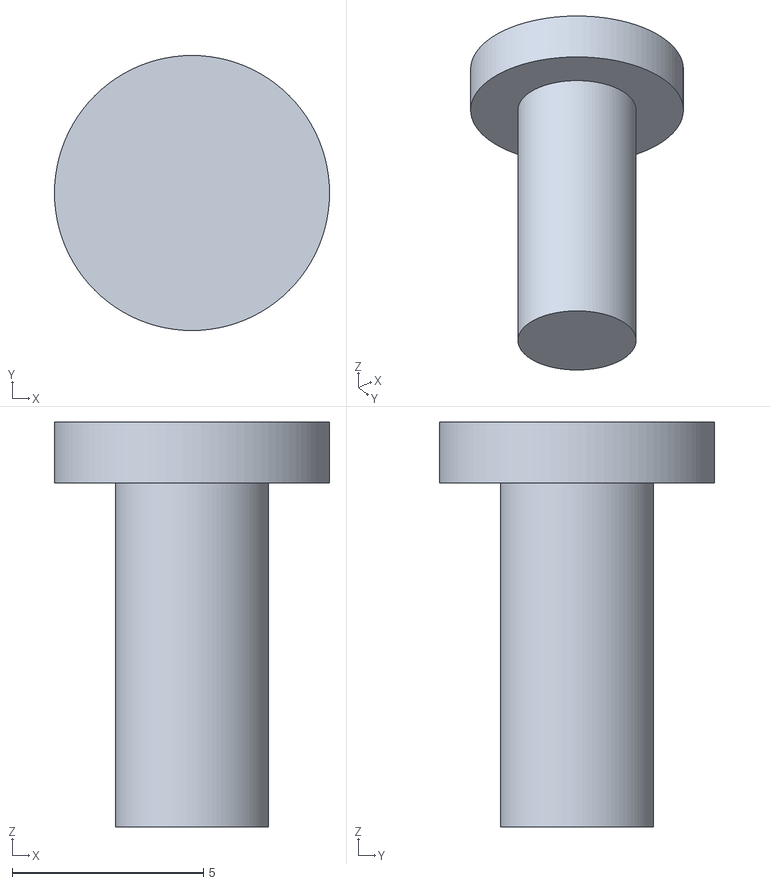
[picture p73: CAD file, 2026-10-01]
designs/rolling-timer-p1s-r2/source/assembly/32_33_module_pin.stl
7.20 x 7.20 x 10.6
