lukacslacko/rolling_clock/designs/rolling-timer-p1s-r2/STL/25_open_pendulum_bob.stl

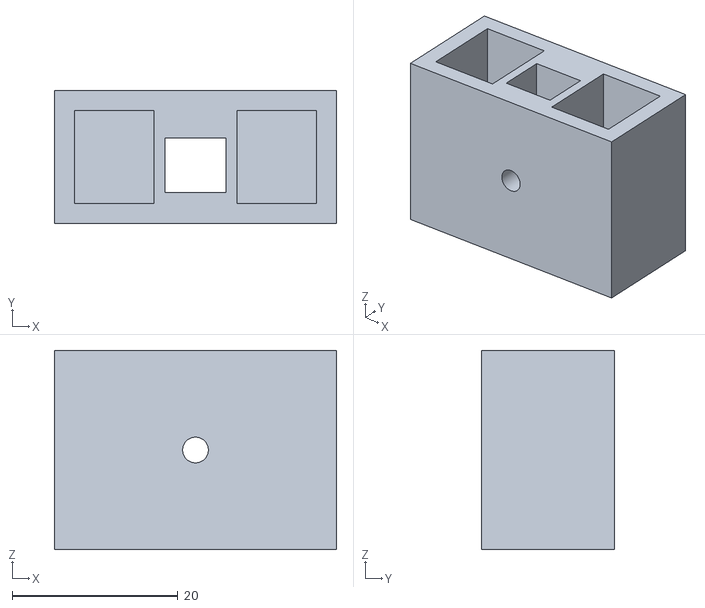
[picture p74: CAD file, 2026-10-01]
designs/rolling-timer-p1s-r2/STL/25_open_pendulum_bob.stl
34.0 x 16.0 x 24.0
