lukacslacko/rolling_clock/designs/rolling-timer-p1s-r2/upgrade-32x/STL/U03_D_18_36_compound.stl

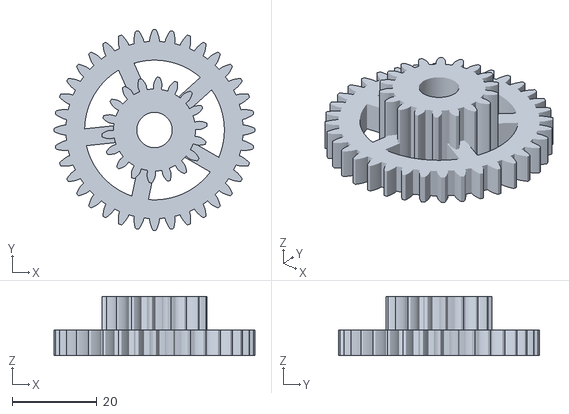
[picture p75: CAD file, 2026-10-01]
designs/rolling-timer-p1s-r2/upgrade-32x/STL/U03_D_18_36_compound.stl
47.5 x 47.5 x 14.0
