lukacslacko/rolling_clock/designs/rolling-timer-r3/assembly/16x/62_B_pivot.stl

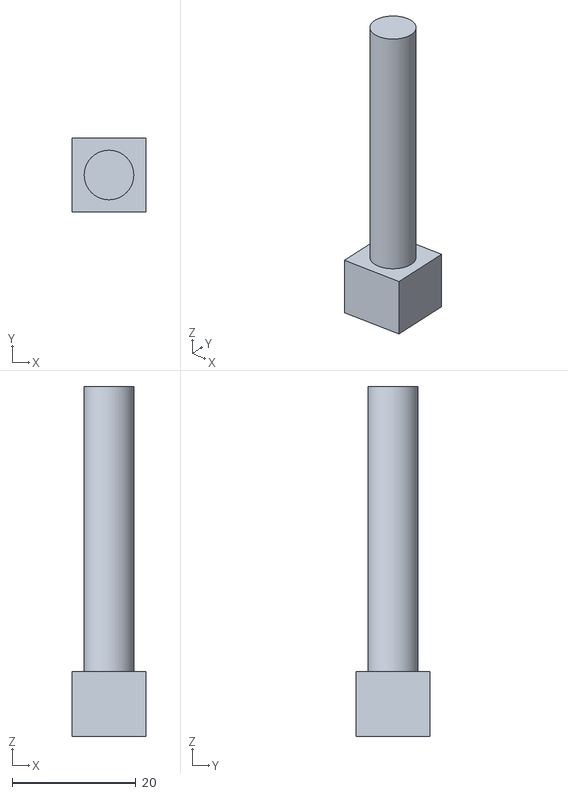
[picture p76: CAD file, 2026-10-07]
designs/rolling-timer-r3/assembly/16x/62_B_pivot.stl
12.0 x 12.0 x 56.5
