lukacslacko/rolling_clock/designs/rolling-timer-r3/assembly/32x/87_bridge_post_0.stl

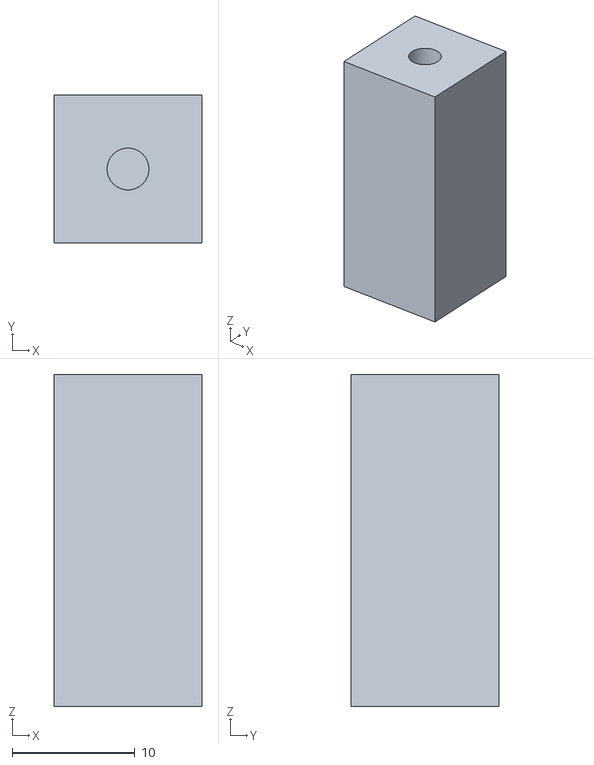
[picture p77: CAD file, 2026-10-07]
designs/rolling-timer-r3/assembly/32x/87_bridge_post_0.stl
12.0 x 12.0 x 27.0
