lukacslacko/rolling_clock/designs/rolling-timer-r3/STL/32x/15_B_rear_spacer.stl

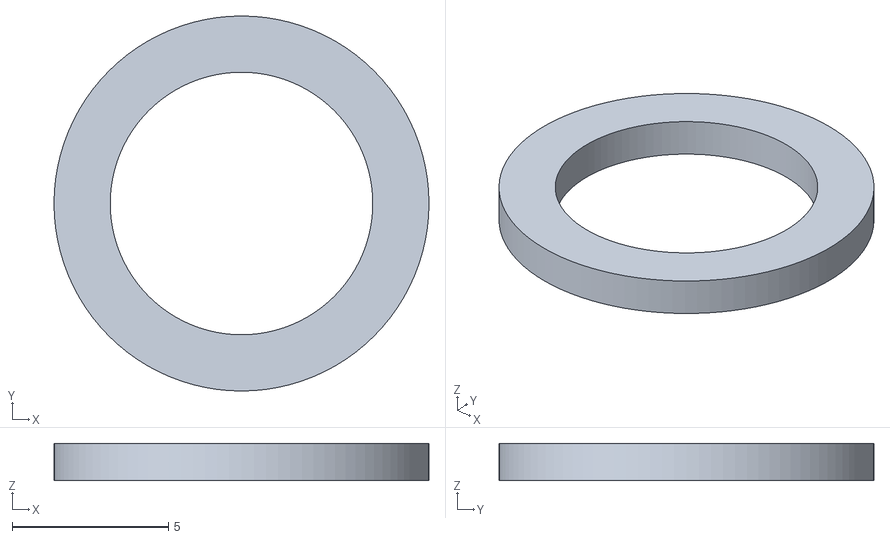
[picture p78: CAD file, 2026-10-02]
designs/rolling-timer-r3/STL/32x/15_B_rear_spacer.stl
12.0 x 12.0 x 1.20
