lukacslacko/rolling_clock/designs/rolling-timer-r3/STL/64x/29_D_front_spacer.stl

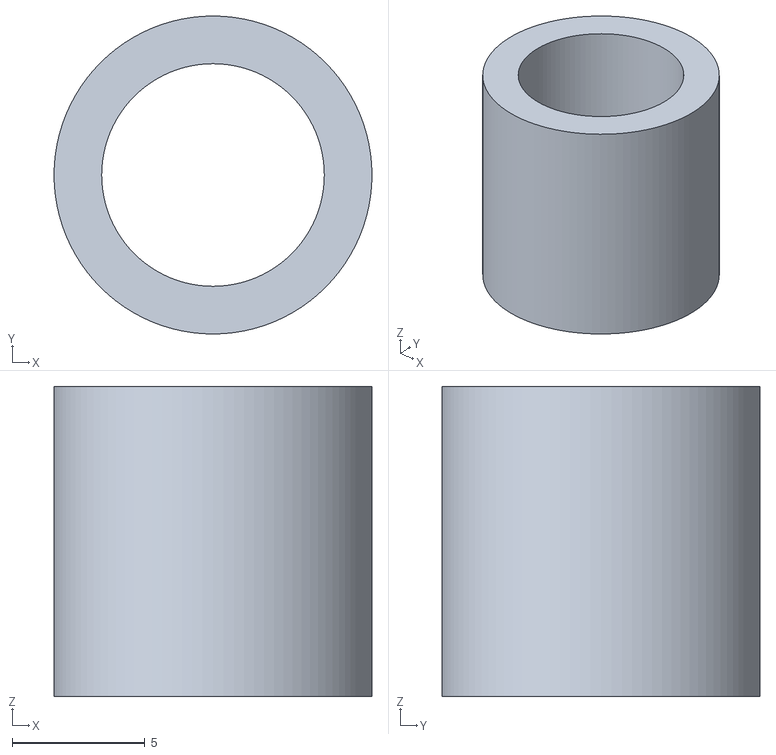
[picture p79: CAD file, 2026-10-02]
designs/rolling-timer-r3/STL/64x/29_D_front_spacer.stl
12.0 x 12.0 x 11.7
