lukacslacko/rolling_clock/designs/rolling-timer-p1s-r2/source/assembly/49_26_bob_pin.stl

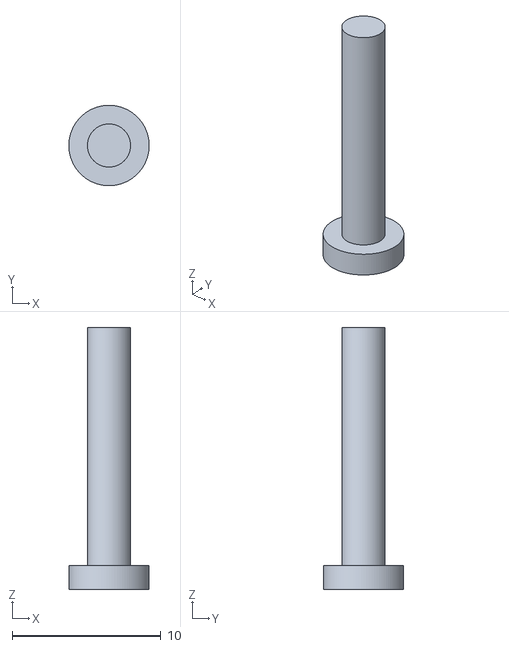
[picture p80: CAD file, 2026-10-01]
designs/rolling-timer-p1s-r2/source/assembly/49_26_bob_pin.stl
5.40 x 5.40 x 17.6
