lukacslacko/rolling_clock/designs/rolling-timer-p1s-r2/upgrade-32x/STL/U08_C_front_spacer.stl

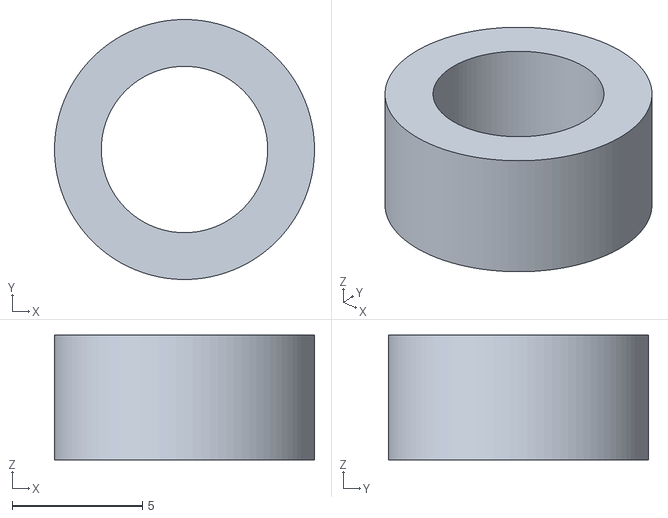
[picture p81: CAD file, 2026-10-01]
designs/rolling-timer-p1s-r2/upgrade-32x/STL/U08_C_front_spacer.stl
10.0 x 10.0 x 4.80
