lukacslacko/rolling_clock/designs/rolling-timer-p1s-light/STL/19_anchor_pivot.stl

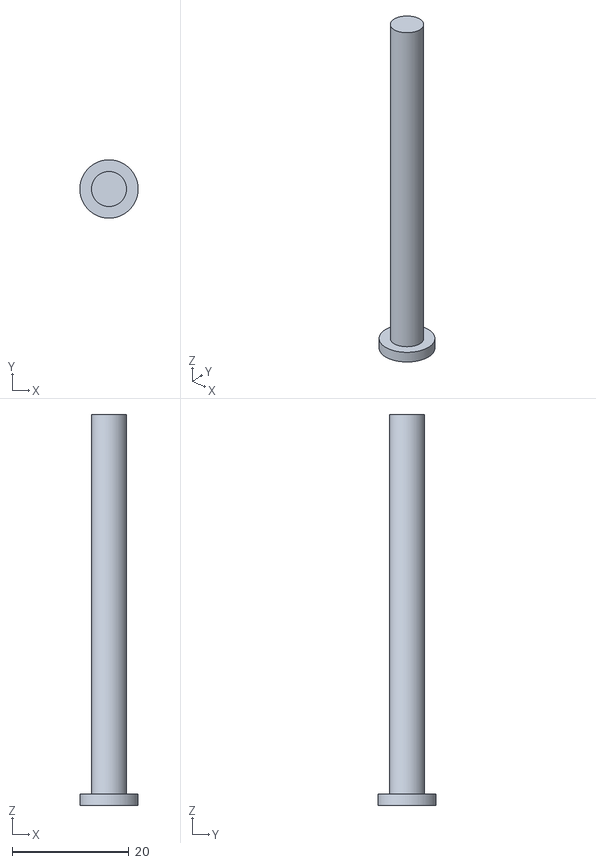
[picture p82: CAD file, 2026-10-01]
designs/rolling-timer-p1s-light/STL/19_anchor_pivot.stl
10.0 x 10.0 x 67.0
