lukacslacko/rolling_clock/designs/rolling-timer-p1s-r2/STL/37_front_round_journal.stl

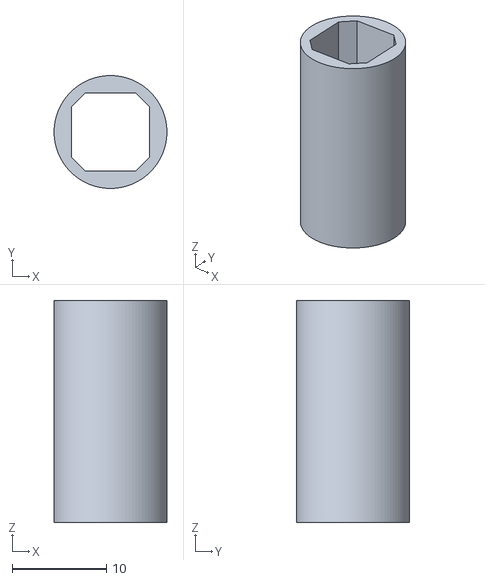
[picture p83: CAD file, 2026-10-01]
designs/rolling-timer-p1s-r2/STL/37_front_round_journal.stl
12.0 x 12.0 x 23.6
