lukacslacko/rolling_clock/designs/rolling-timer-p1s-r2/upgrade-32x/STL/U07_C_rear_spacer.stl

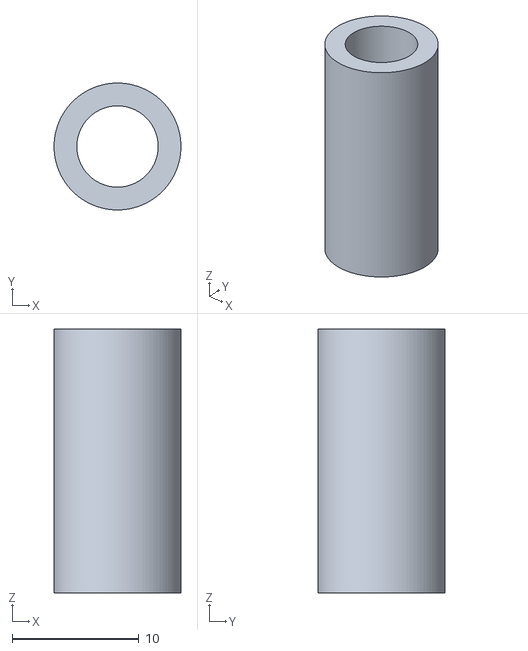
[picture p84: CAD file, 2026-10-01]
designs/rolling-timer-p1s-r2/upgrade-32x/STL/U07_C_rear_spacer.stl
10.0 x 10.0 x 20.8
