lukacslacko/rolling_clock/designs/rolling-timer-r3/assembly/16x/40_06_shared_front_frame.stl

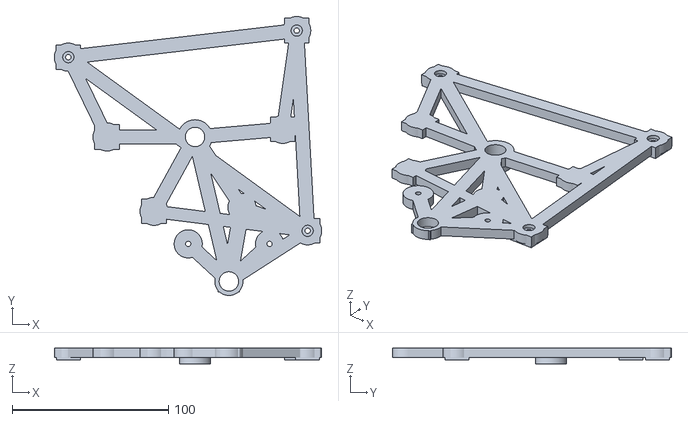
[picture p85: CAD file, 2026-10-07]
designs/rolling-timer-r3/assembly/16x/40_06_shared_front_frame.stl
171.0 x 178.4 x 10.0
