lukacslacko/rolling_clock/designs/rolling-timer-r3/STL/common/36_rear_round_journal.stl

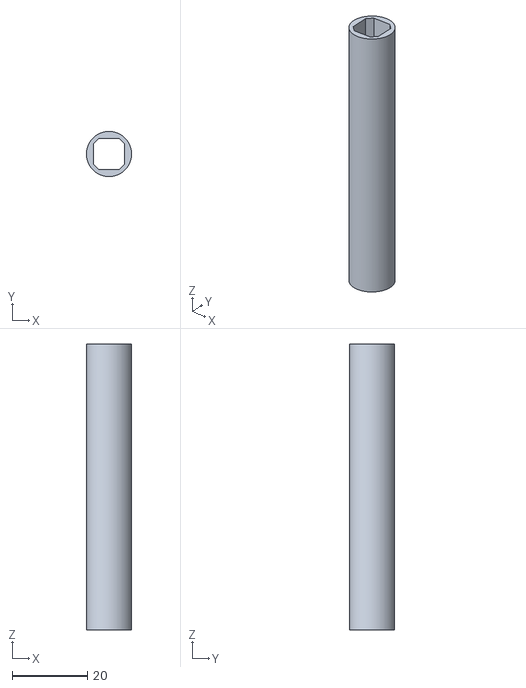
[picture p86: CAD file, 2026-10-07]
designs/rolling-timer-r3/STL/common/36_rear_round_journal.stl
12.0 x 12.0 x 76.0
