lukacslacko/rolling_clock/designs/rolling-timer-p1s-r2/upgrade-32x/STL/U06_B_front_spacer.stl

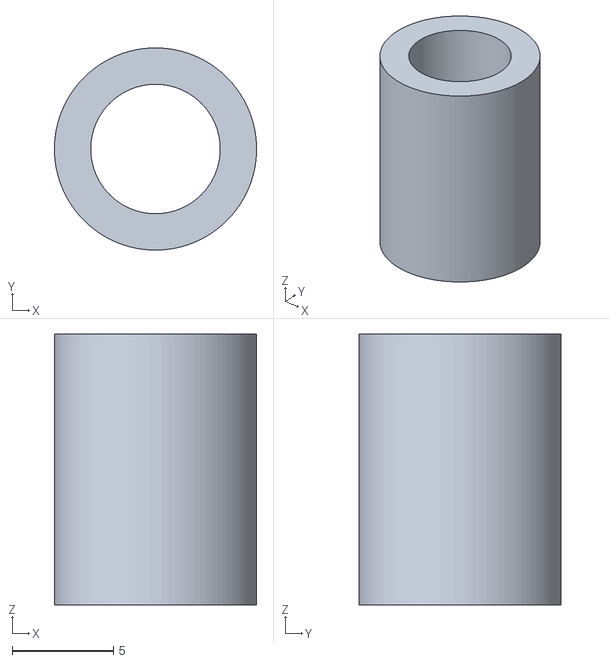
[picture p87: CAD file, 2026-10-01]
designs/rolling-timer-p1s-r2/upgrade-32x/STL/U06_B_front_spacer.stl
10.0 x 10.0 x 13.4
