lukacslacko/rolling_clock/designs/rolling-timer-r3/assembly/32x/85_21_anchor_front_spacer.stl

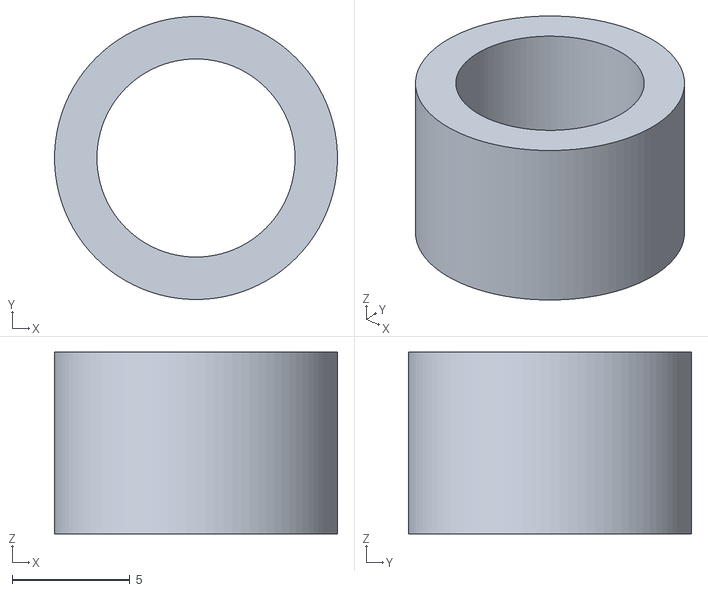
[picture p88: CAD file, 2026-10-07]
designs/rolling-timer-r3/assembly/32x/85_21_anchor_front_spacer.stl
12.0 x 12.0 x 7.70
