lukacslacko/rolling_clock/designs/rolling-timer-r3/STL/common/24_offset_pendulum.stl

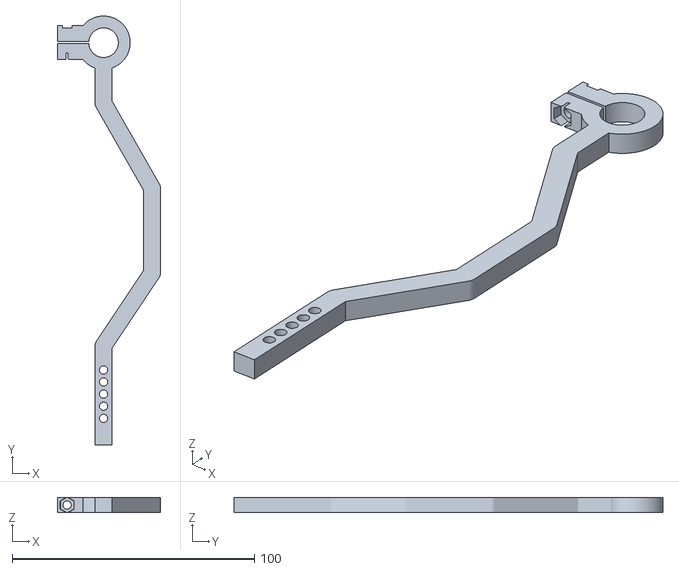
[picture p89: CAD file, 2026-10-02]
designs/rolling-timer-r3/STL/common/24_offset_pendulum.stl
42.5 x 177.0 x 6.00
