lukacslacko/rolling_clock/designs/rolling-timer-p1s-light/STL/16_C_rear_spacer.stl

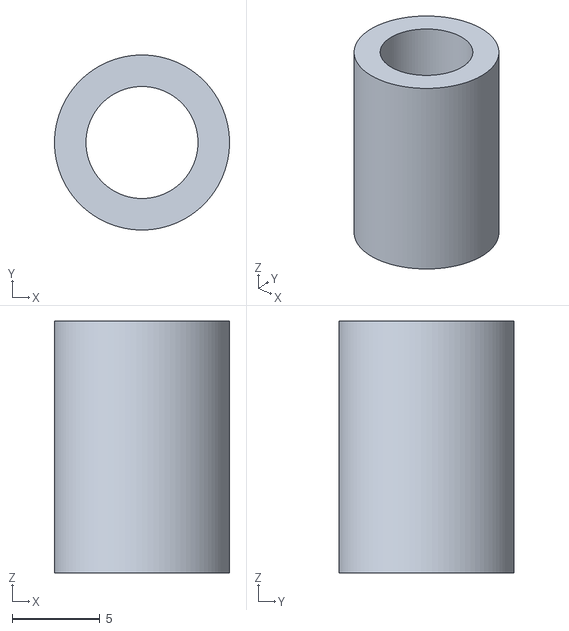
[picture p90: CAD file, 2026-10-01]
designs/rolling-timer-p1s-light/STL/16_C_rear_spacer.stl
10.0 x 10.0 x 14.4
