lukacslacko/rolling_clock/designs/rolling-timer-p1s-r2/STL/10_drive_72.stl

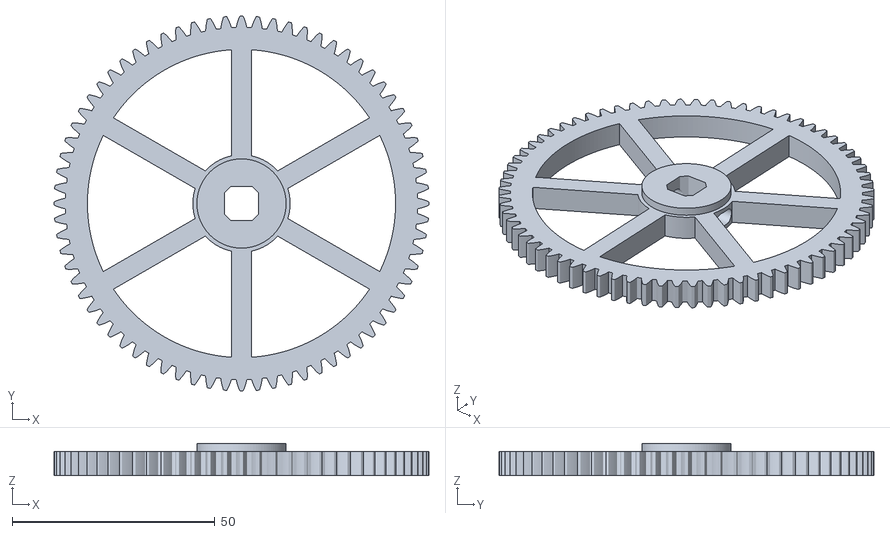
[picture p91: CAD file, 2026-10-01]
designs/rolling-timer-p1s-r2/STL/10_drive_72.stl
92.5 x 92.5 x 8.00
