lukacslacko/rolling_clock/designs/rolling-timer-p1s-r2/upgrade-32x/STL/U01_BD_rear_module.stl

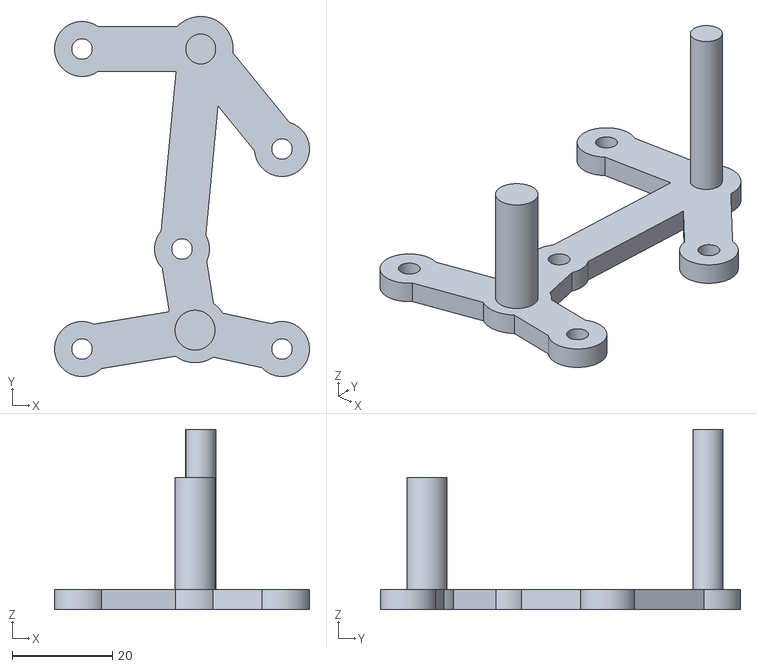
[picture p92: CAD file, 2026-10-01]
designs/rolling-timer-p1s-r2/upgrade-32x/STL/U01_BD_rear_module.stl
51.0 x 72.0 x 36.0
