lukacslacko/rolling_clock/designs/rolling-timer-r3/assembly/32x/17_case_post_4.stl

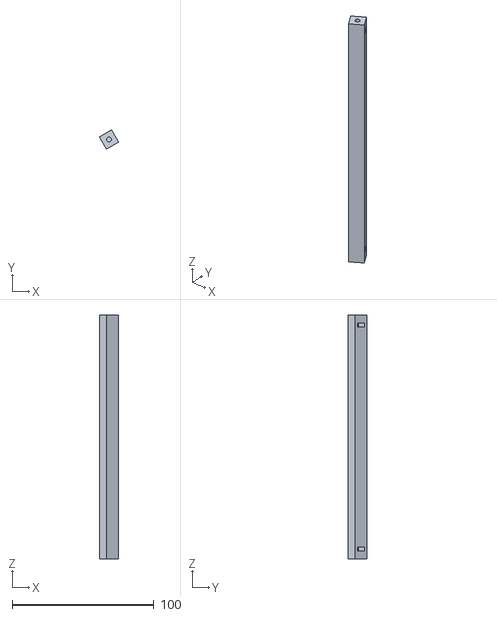
[picture p93: CAD file, 2026-10-07]
designs/rolling-timer-r3/assembly/32x/17_case_post_4.stl
13.7 x 13.7 x 172.0
