lukacslacko/rolling_clock/designs/rolling-timer-p1s-light/source/assembly/37_36_rear_round_journal.stl

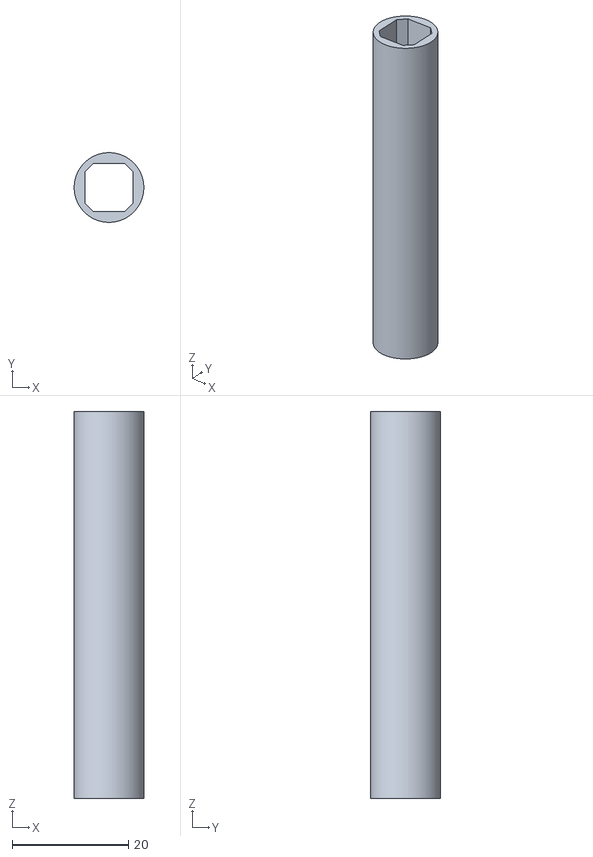
[picture p94: CAD file, 2026-10-01]
designs/rolling-timer-p1s-light/source/assembly/37_36_rear_round_journal.stl
12.0 x 12.0 x 66.6
