lukacslacko/rolling_clock/designs/rolling-timer-r3/STL/common/10_drive_72.stl

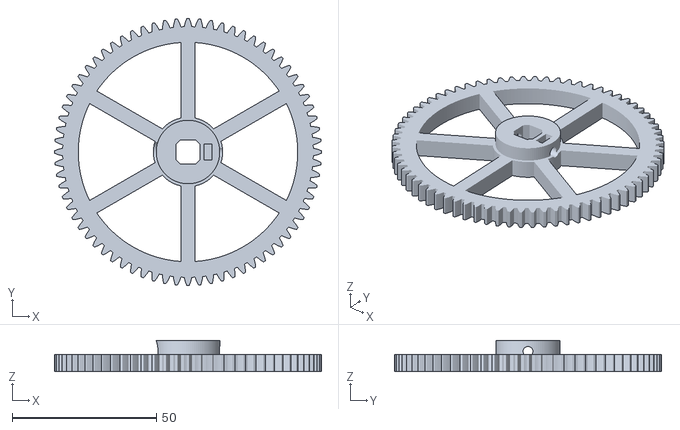
[picture p96: CAD file, 2026-10-02]
designs/rolling-timer-r3/STL/common/10_drive_72.stl
92.5 x 92.5 x 10.8
