lukacslacko/rolling_clock/designs/rolling-timer-p1s-r2/source/assembly/44_22_anchor_bridge.stl

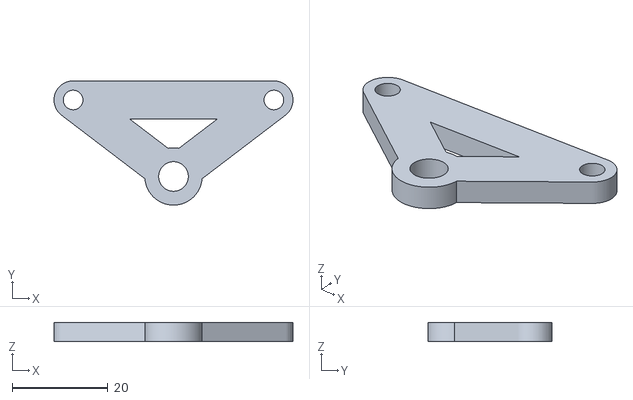
[picture p97: CAD file, 2026-10-01]
designs/rolling-timer-p1s-r2/source/assembly/44_22_anchor_bridge.stl
50.0 x 26.0 x 4.00
