lukacslacko/rolling_clock/designs/rolling-timer-p1s-r2/STL/32_B_front_pivot_module.stl

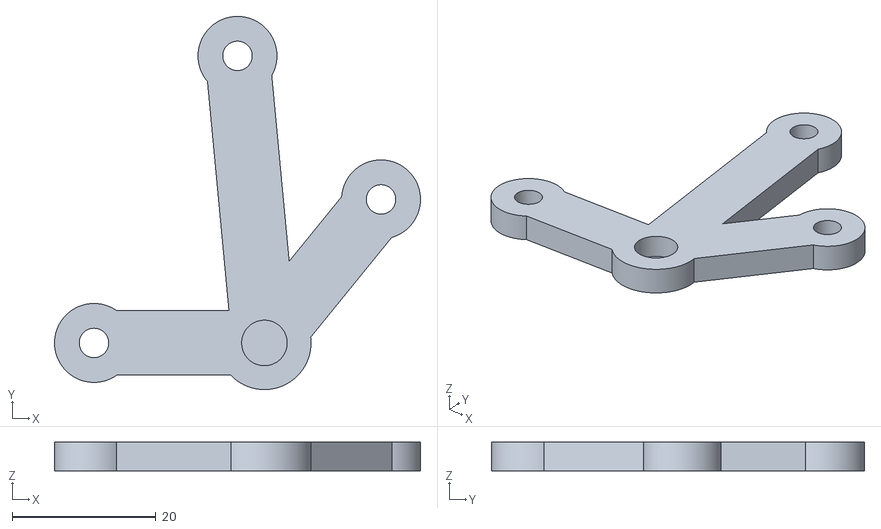
[picture p98: CAD file, 2026-10-01]
designs/rolling-timer-p1s-r2/STL/32_B_front_pivot_module.stl
51.0 x 52.0 x 4.00
