lukacslacko/rolling_clock/designs/rolling-timer-r3/assembly/16x/78_20_anchor_rear_spacer.stl

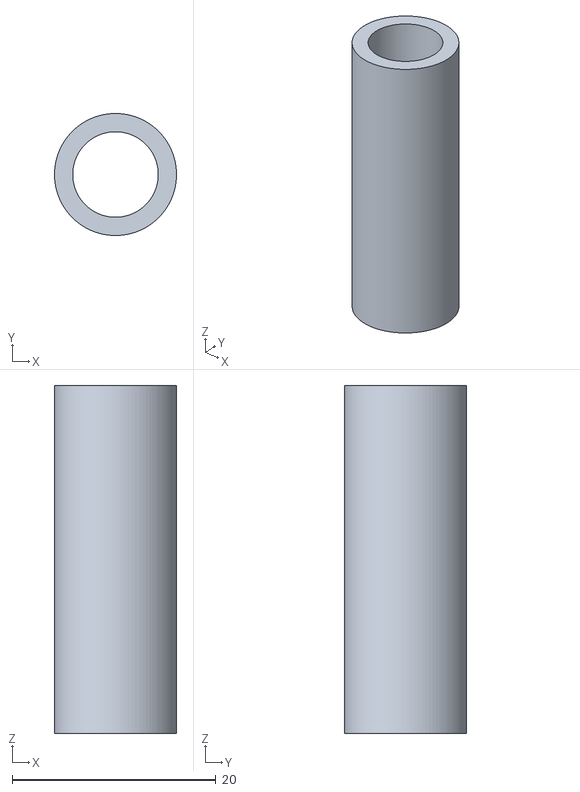
[picture p99: CAD file, 2026-10-07]
designs/rolling-timer-r3/assembly/16x/78_20_anchor_rear_spacer.stl
12.0 x 12.0 x 34.2
