lukacslacko/rolling_clock/designs/rolling-timer-r3/STL/common/08_open_ballast_bowl.stl

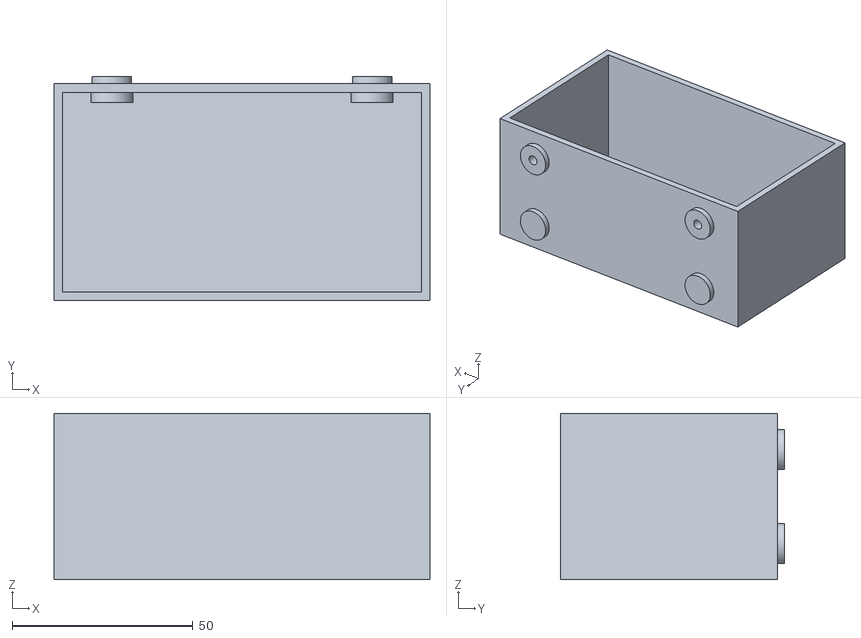
[picture p100: CAD file, 2026-10-02]
designs/rolling-timer-r3/STL/common/08_open_ballast_bowl.stl
104.0 x 62.0 x 46.0
