lukacslacko/rolling_clock/designs/rolling-timer-p1s-light/source/assembly/34_24_pendulum.stl

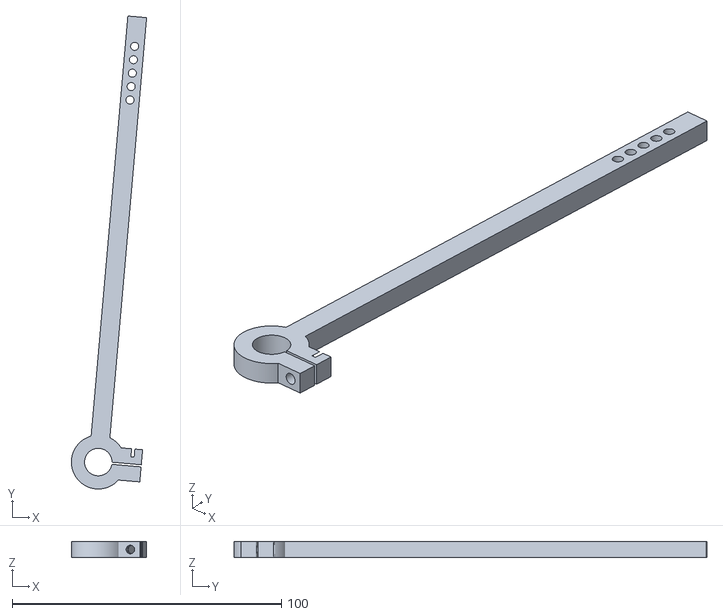
[picture p101: CAD file, 2026-10-01]
designs/rolling-timer-p1s-light/source/assembly/34_24_pendulum.stl
28.0 x 175.7 x 6.00
