lukacslacko/rolling_clock/designs/rolling-timer-p1s-light/bench-guide/renders/gear-stacks.png

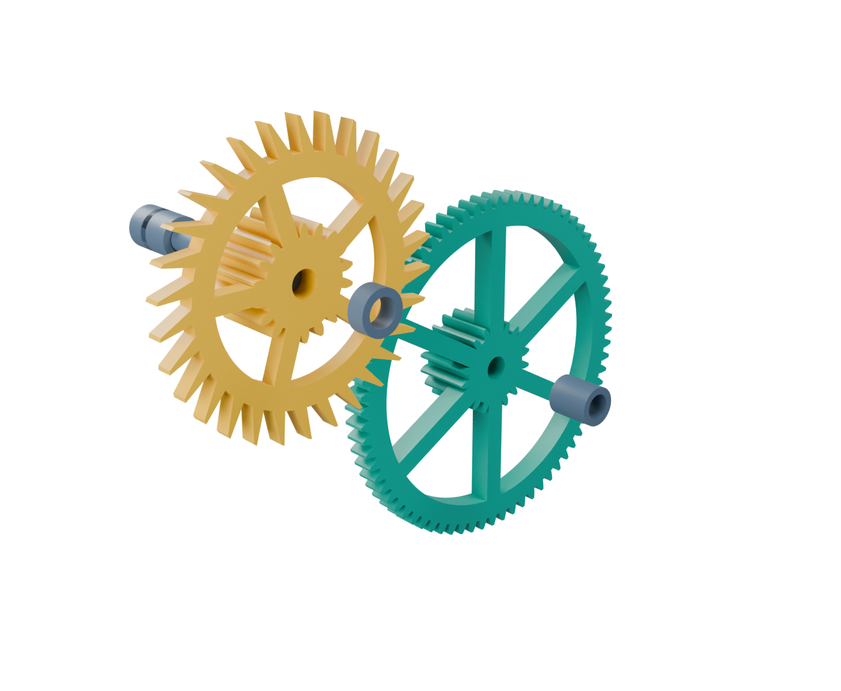
designs/rolling-timer-p1s-light/bench-guide/renders/gear-stacks.png
