lukacslacko/rolling_clock/designs/rolling-timer-p1s-r2/renders/compound-gears-on-print-faces.png

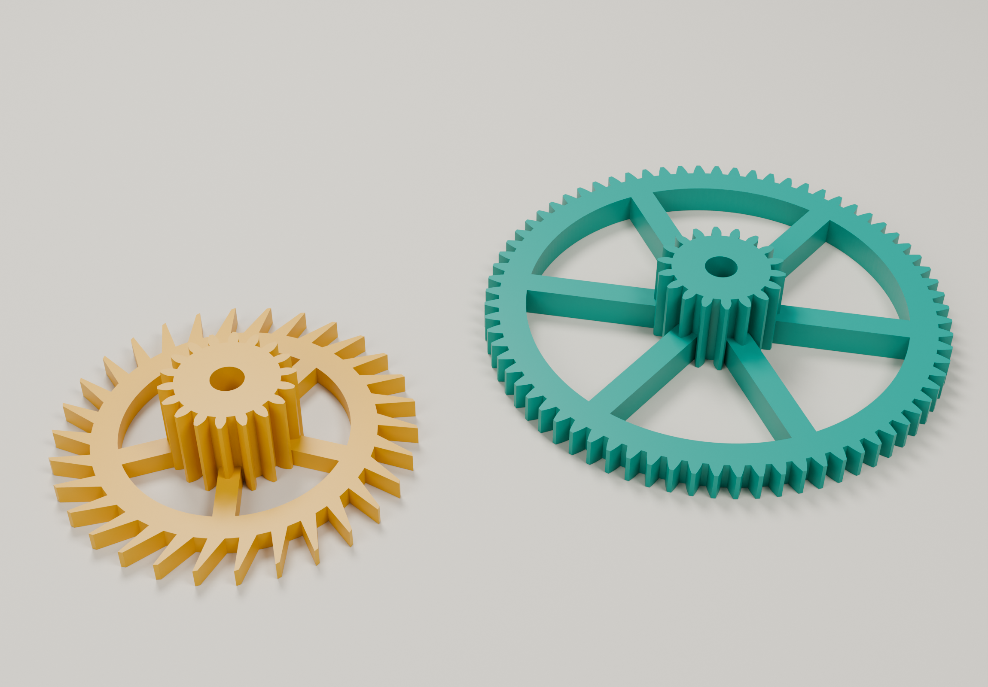
designs/rolling-timer-p1s-r2/renders/compound-gears-on-print-faces.png
